bombons/cad-eggbot/progetto/1.png

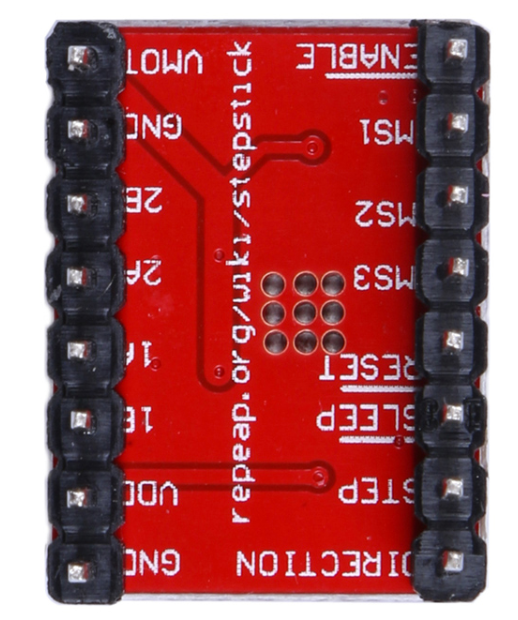
progetto/1.png
