bombons/cad-eggbot/progetto/2.png

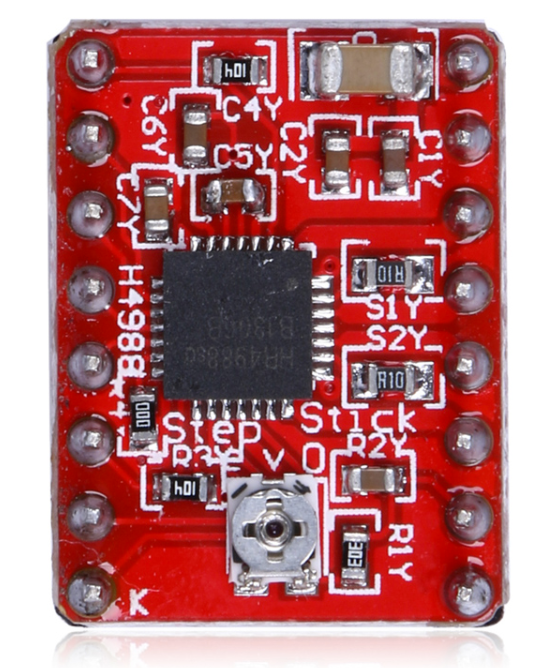
progetto/2.png
