bombons/cad-eggbot/progetto/6pin_header.SLDASM

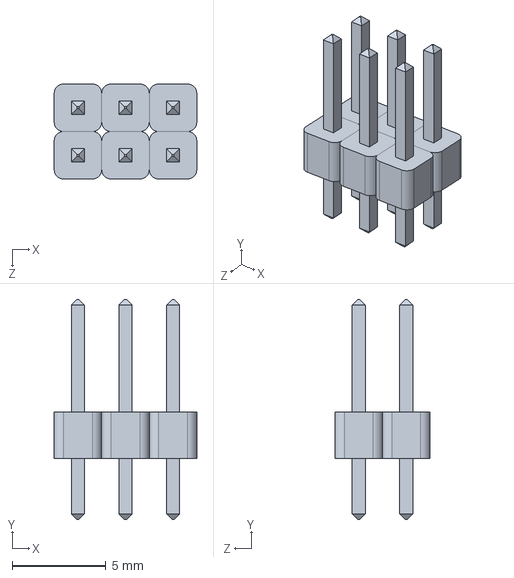
[picture p24: CAD file, 2019-10-07]
progetto/6pin_header.SLDASM
7.62 x 11.8 x 5.08 mm
pin_header x 2
