bombons/cad-eggbot/progetto/statore_spazzole.SLDPRT

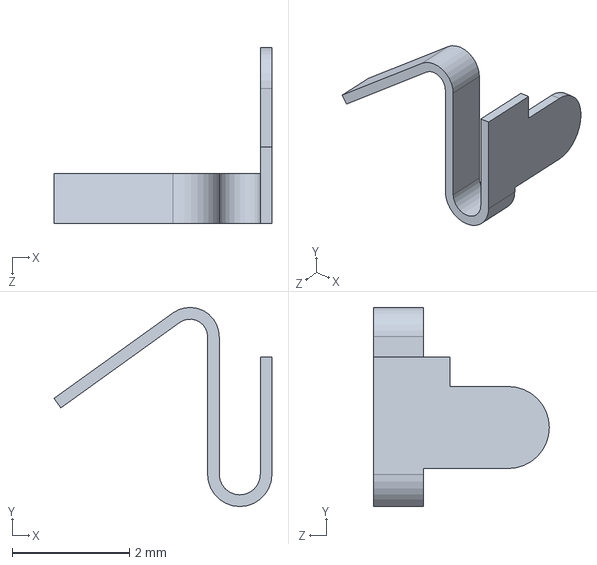
[picture p25: CAD file, 2019-10-07]
progetto/statore_spazzole.SLDPRT
3.72 x 3.40 x 3.00 mm
