bombons/cad-eggbot/progetto/dietro.SLDPRT

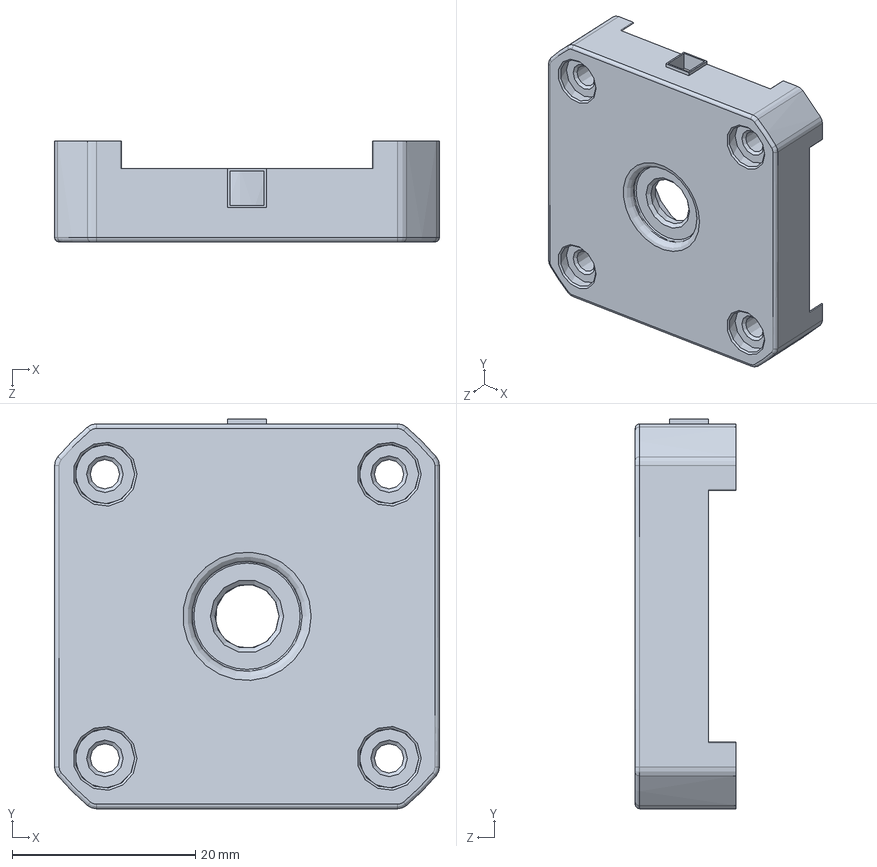
[picture p26: CAD file, 2019-10-07]
progetto/dietro.SLDPRT
42.0 x 42.5 x 11.0 mm
