bombons/cad-eggbot/progetto/pomello_barra_filettata.SLDPRT

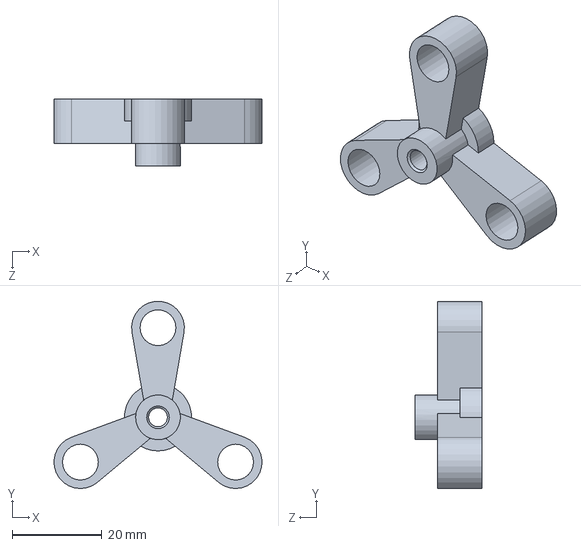
[picture p27: CAD file, 2019-10-07]
progetto/pomello_barra_filettata.SLDPRT
46.4 x 41.8 x 15.0 mm
