bombons/cad-eggbot/progetto/usb_shell.sldprt

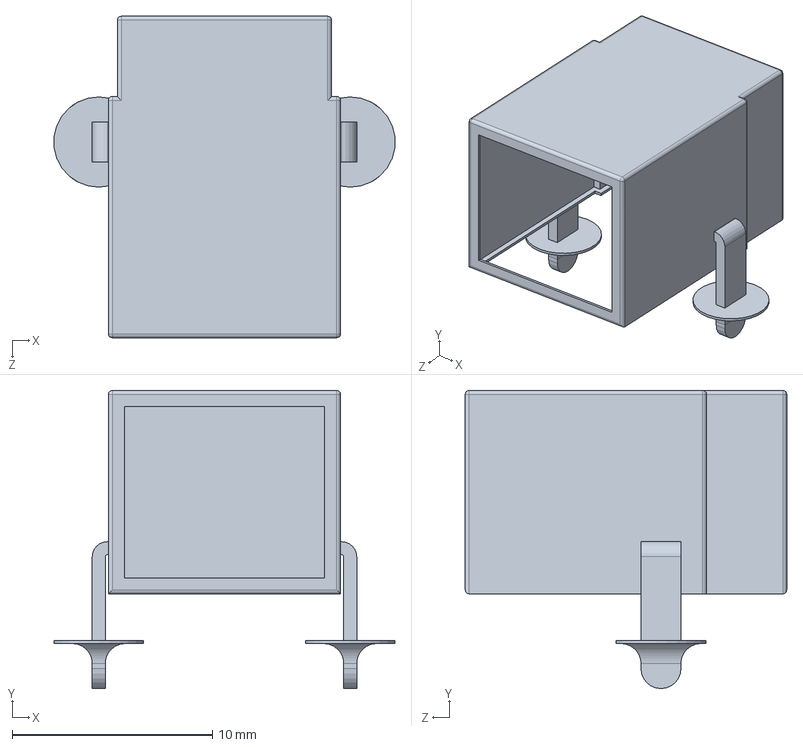
[picture p28: CAD file, 2019-10-07]
progetto/usb_shell.sldprt
17.0 x 14.9 x 16.0 mm
