bombons/cad-eggbot/progetto/jack_alimentazione.SLDPRT

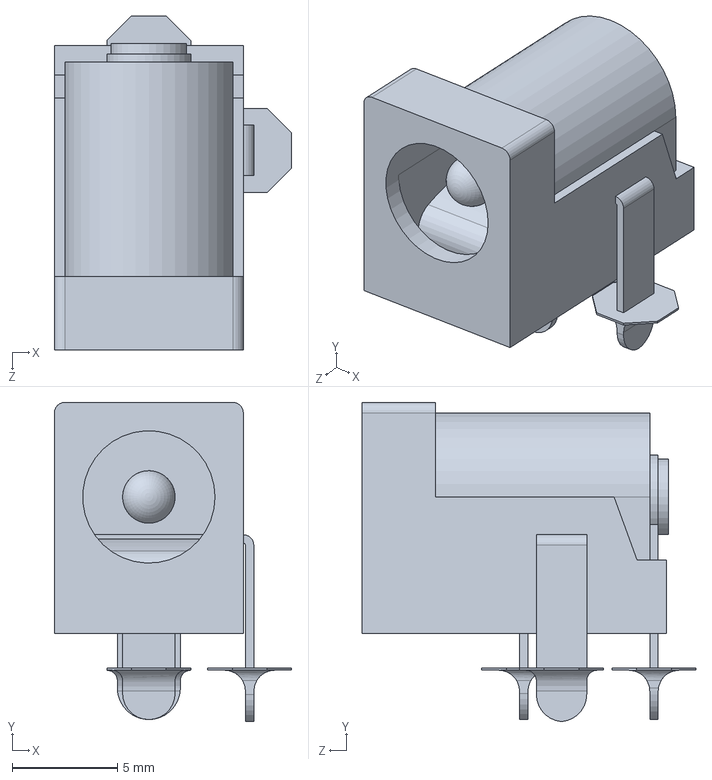
[picture p29: CAD file, 2019-10-07]
progetto/jack_alimentazione.SLDPRT
11.3 x 15.2 x 15.9 mm
