bombons/cad-eggbot/progetto/statore_molla.SLDPRT

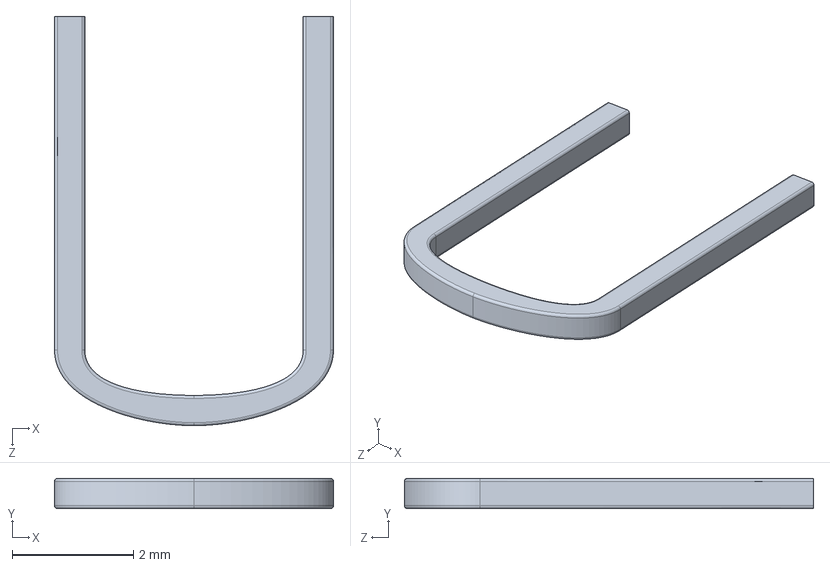
[picture p30: CAD file, 2019-10-07]
progetto/statore_molla.SLDPRT
4.60 x 0.5 x 6.75 mm
