bombons/cad-eggbot/progetto/asse.SLDPRT

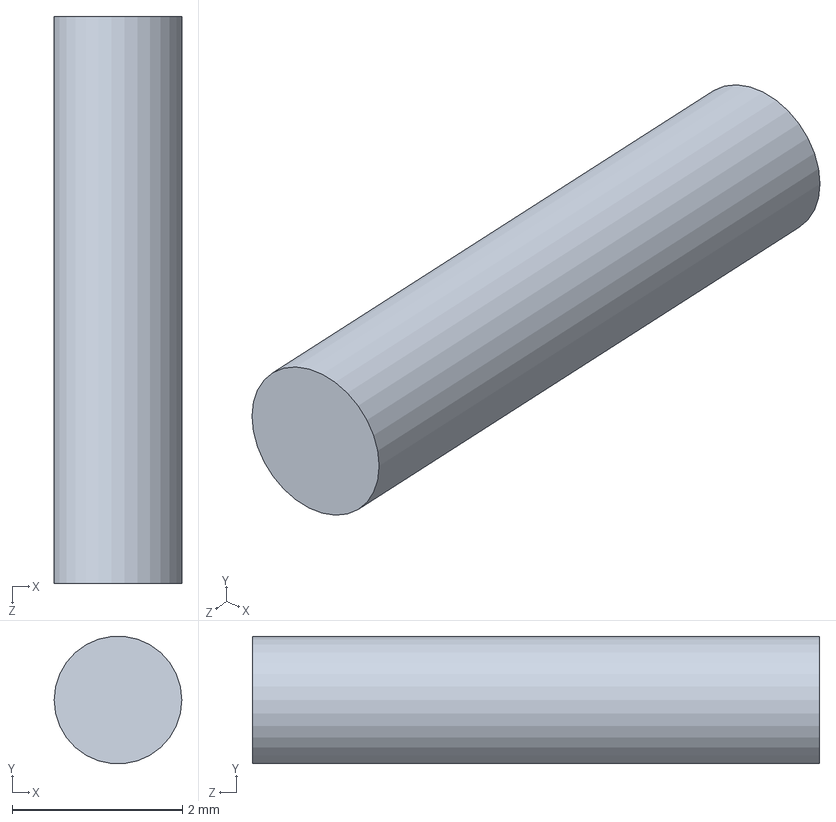
[picture p31: CAD file, 2019-10-07]
progetto/asse.SLDPRT
1.50 x 1.49 x 6.66 mm
