bombons/cad-eggbot/progetto/crystal.SLDPRT

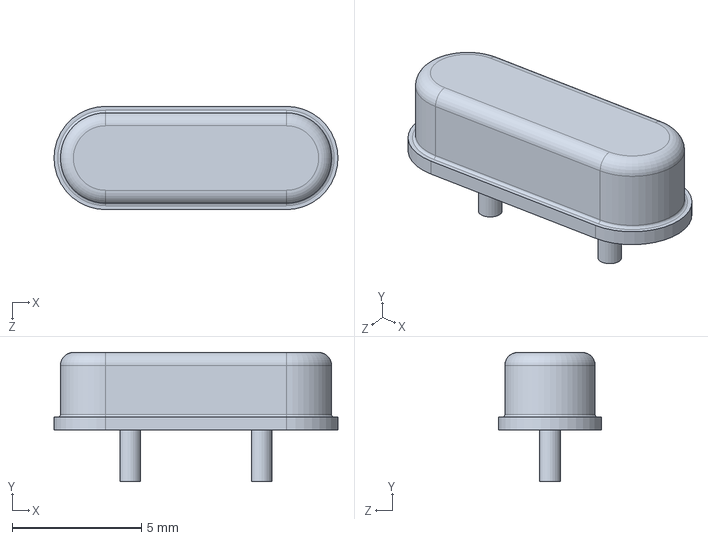
[picture p32: CAD file, 2019-10-07]
progetto/crystal.SLDPRT
11.0 x 5.00 x 4.00 mm
