bombons/cad-eggbot/progetto/asse1.SLDPRT

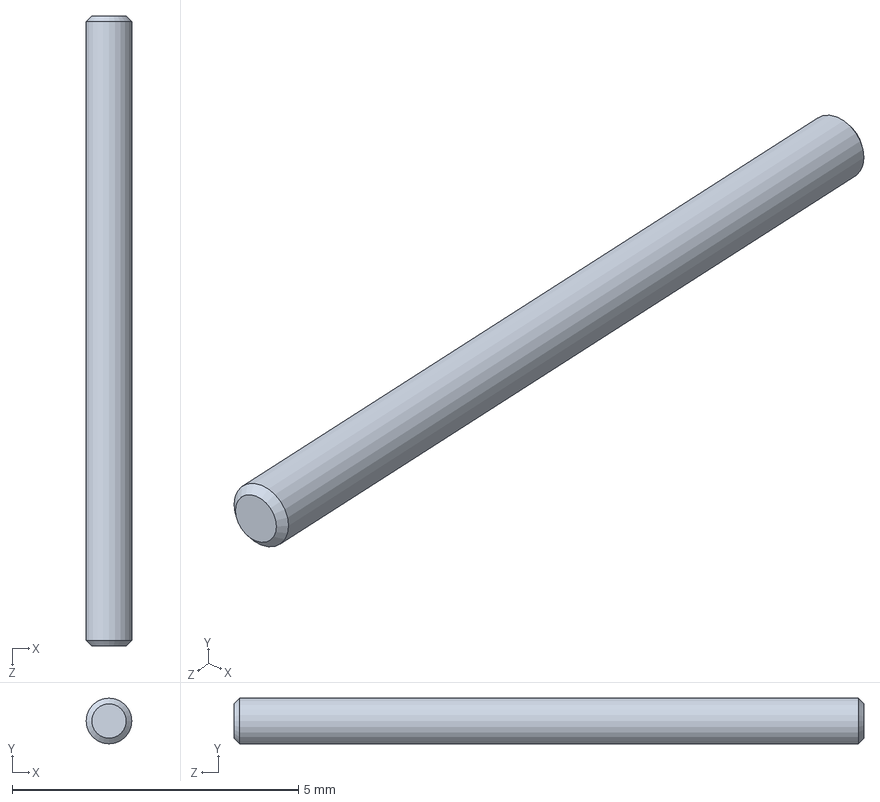
[picture p33: CAD file, 2019-10-07]
progetto/asse1.SLDPRT
0.8 x 0.8 x 11.0 mm
