bombons/cad-eggbot/progetto/board.SLDPRT

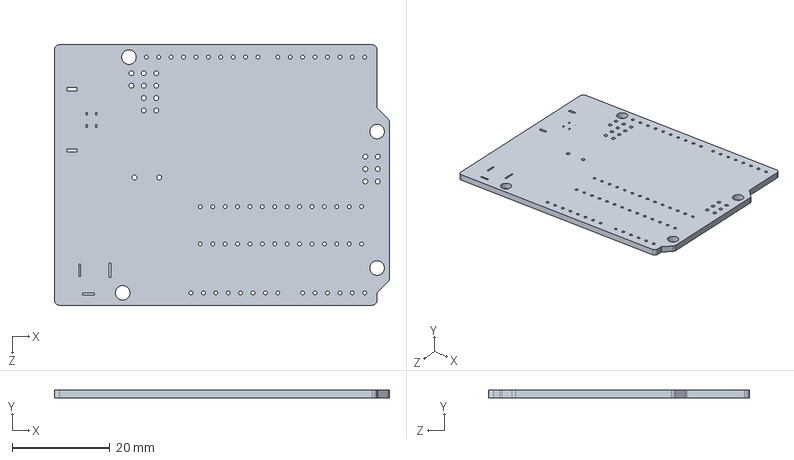
[picture p34: CAD file, 2019-10-07]
progetto/board.SLDPRT
68.6 x 1.65 x 53.3 mm
