bombons/cad-eggbot/progetto/bottone_reset_copertura.SLDPRT

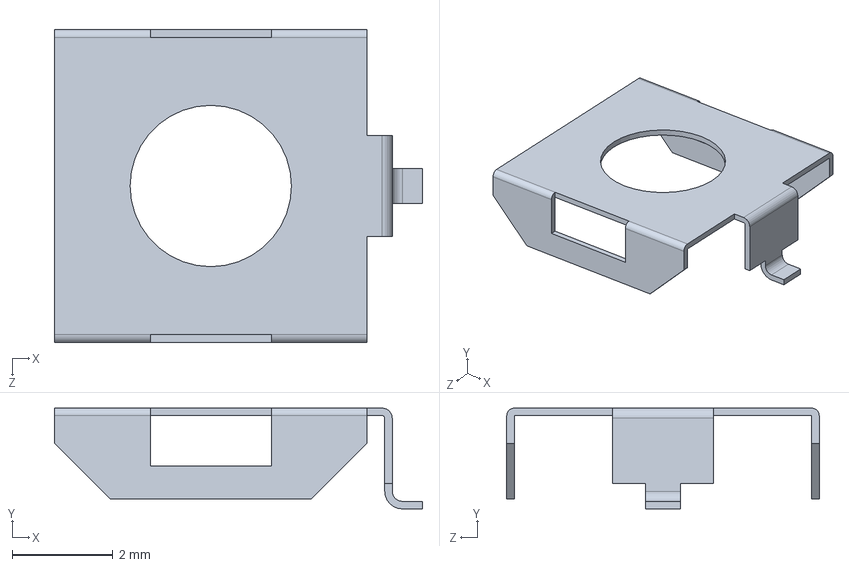
[picture p35: CAD file, 2019-10-07]
progetto/bottone_reset_copertura.SLDPRT
7.30 x 2.00 x 6.20 mm
