bombons/cad-eggbot/progetto/porta_pin.SLDPRT

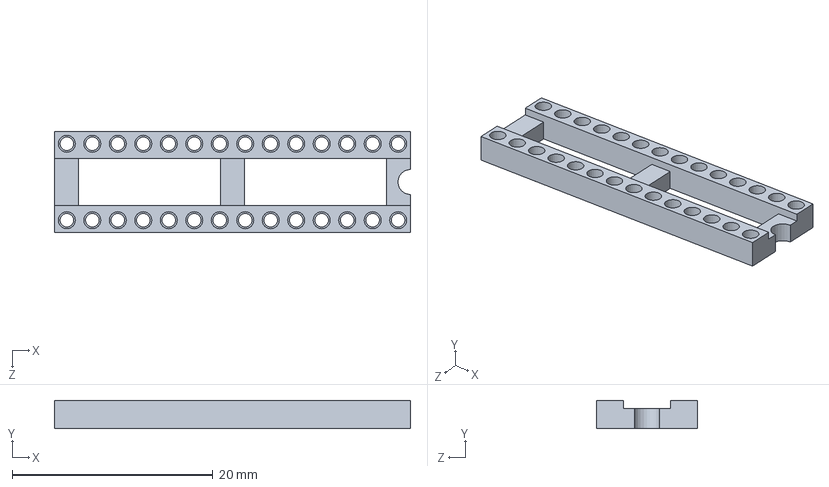
[picture p36: CAD file, 2019-10-07]
progetto/porta_pin.SLDPRT
35.5 x 2.80 x 10.1 mm
