bombons/cad-eggbot/progetto/statore_cuscino1.SLDPRT

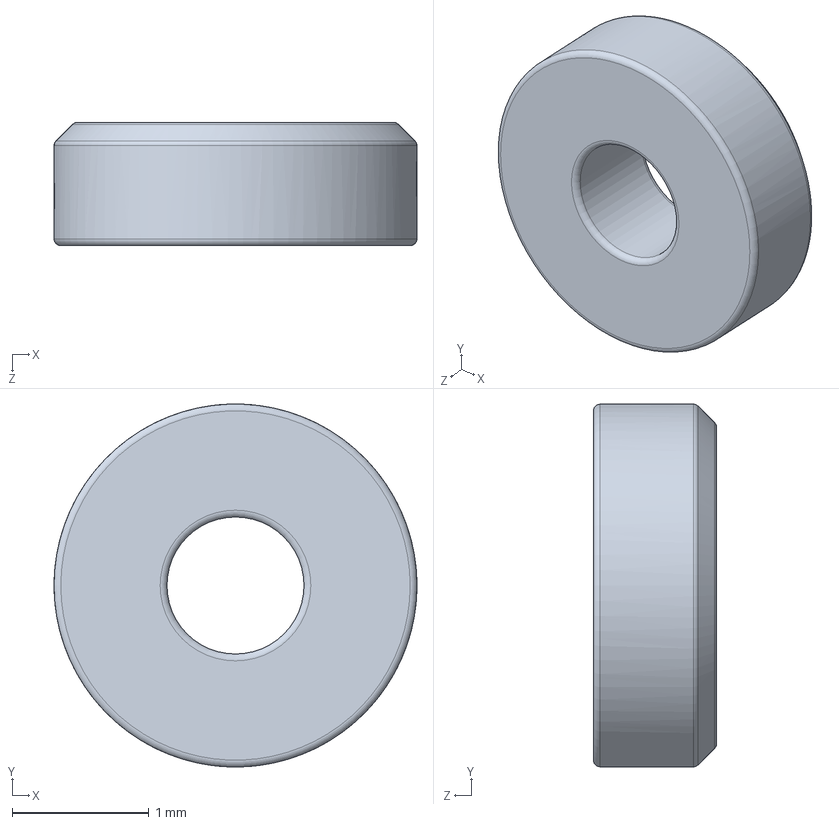
[picture p37: CAD file, 2019-10-07]
progetto/statore_cuscino1.SLDPRT
2.65 x 2.65 x 0.9 mm
