bombons/cad-eggbot/progetto/penna_braccio_fisso.SLDPRT

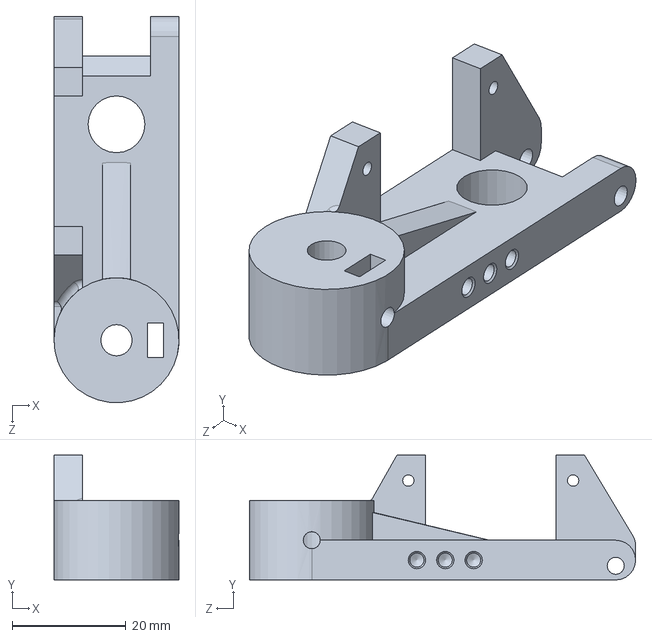
[picture p38: CAD file, 2019-10-07]
progetto/penna_braccio_fisso.SLDPRT
22.0 x 22.0 x 68.0 mm
