bombons/cad-eggbot/progetto/microprocessore.SLDPRT

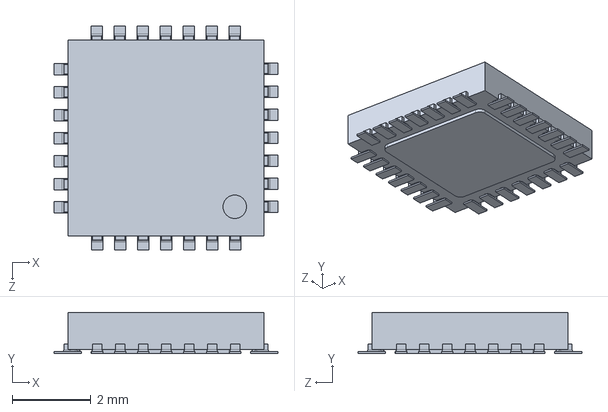
[picture p39: CAD file, 2019-10-07]
progetto/microprocessore.SLDPRT
5.70 x 1.05 x 5.70 mm
