bombons/cad-eggbot/progetto/usb_contatto_su.SLDPRT

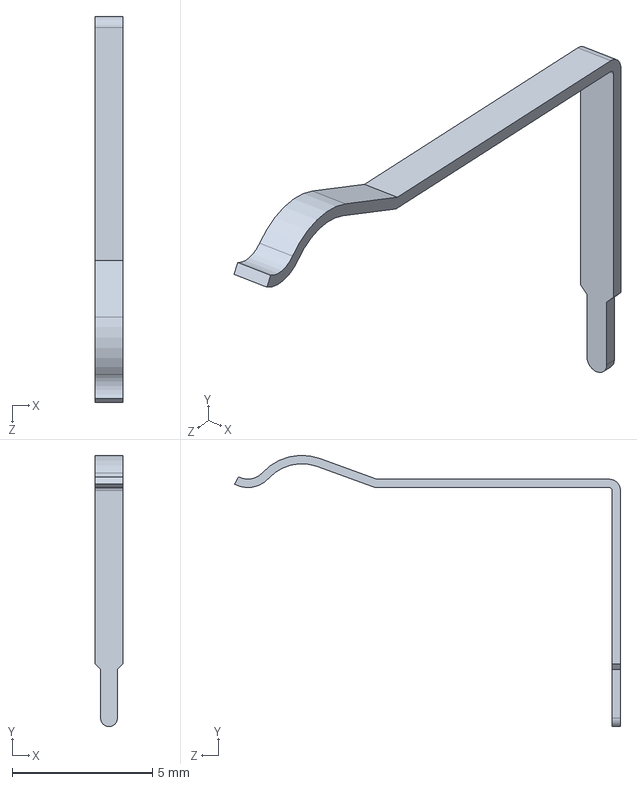
[picture p40: CAD file, 2019-10-07]
progetto/usb_contatto_su.SLDPRT
1.00 x 9.67 x 13.8 mm
