bombons/cad-eggbot/progetto/pot_0.80mm.SLDPRT

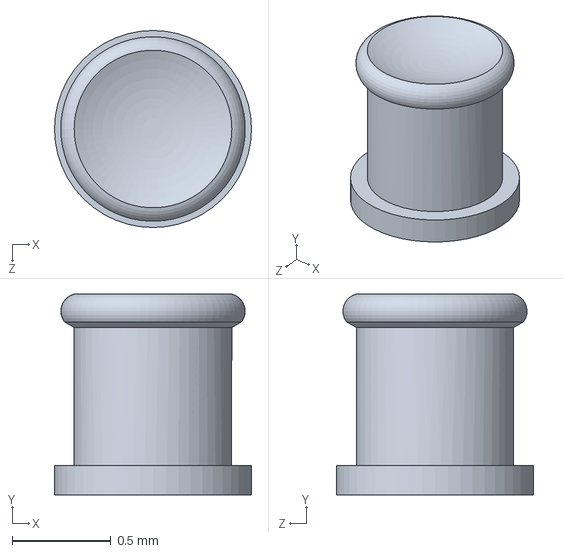
[picture p41: CAD file, 2019-10-07]
progetto/pot_0.80mm.SLDPRT
1.00 x 1.02 x 1.00 mm
