bombons/cad-eggbot/progetto/porta_arduino.SLDPRT

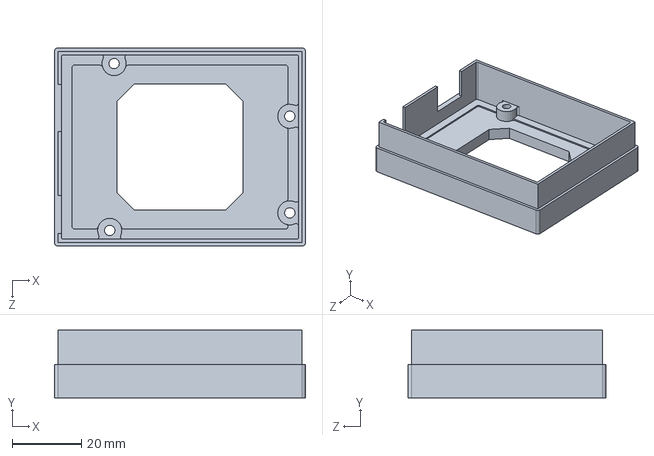
[picture p42: CAD file, 2019-10-07]
progetto/porta_arduino.SLDPRT
72.6 x 19.6 x 57.3 mm
