bombons/cad-eggbot/progetto/1.2_16.SLDPRT

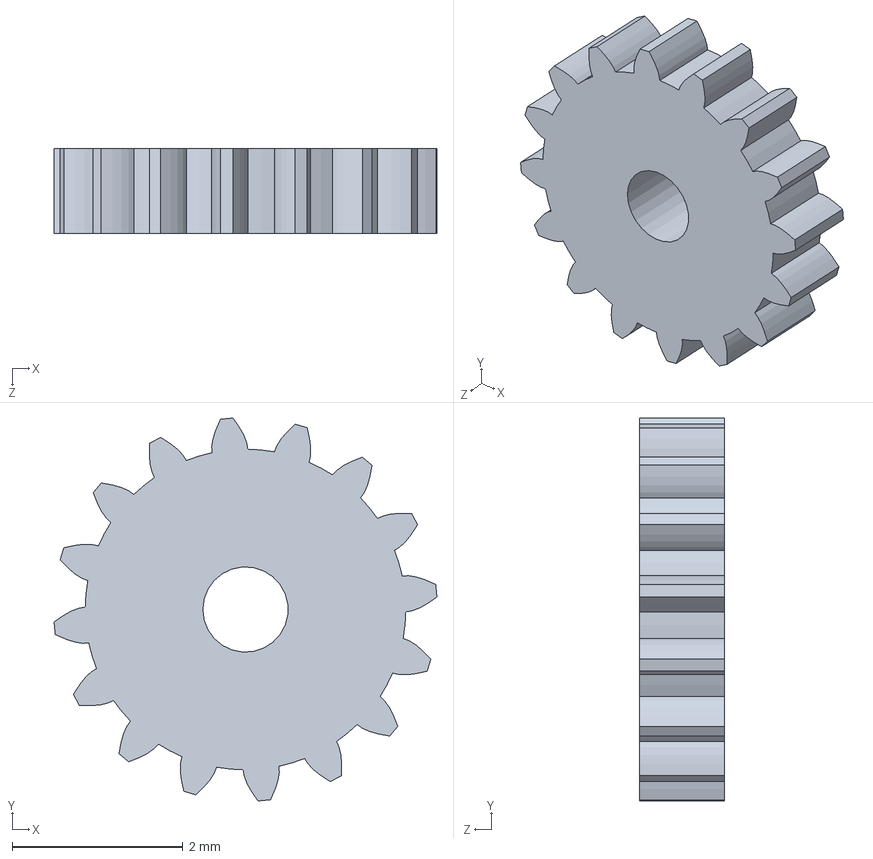
[picture p43: CAD file, 2019-10-07]
progetto/1.2_16.SLDPRT
4.49 x 4.49 x 1.00 mm
