bombons/cad-eggbot/progetto/davanti.SLDPRT

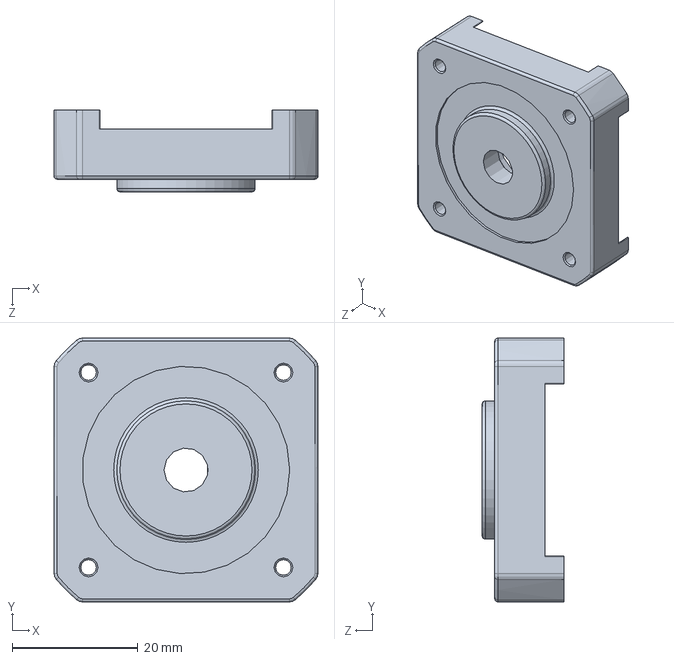
[picture p44: CAD file, 2019-10-07]
progetto/davanti.SLDPRT
42.0 x 42.0 x 13.0 mm
