bombons/cad-eggbot/progetto/1.3_32.SLDPRT

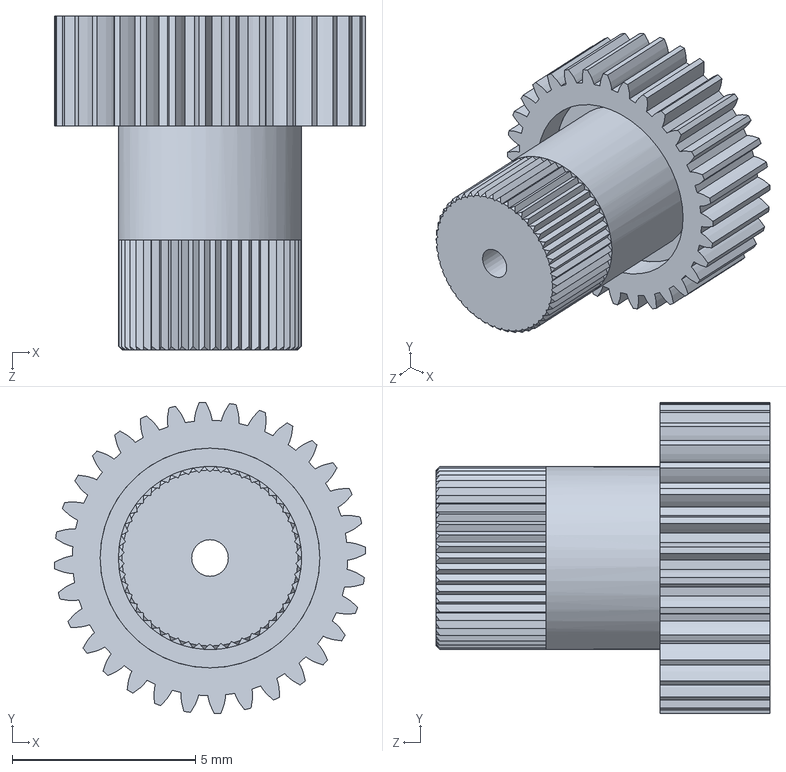
[picture p45: CAD file, 2019-10-07]
progetto/1.3_32.SLDPRT
8.50 x 8.50 x 9.12 mm
