bombons/cad-eggbot/progetto/rotore.SLDPRT

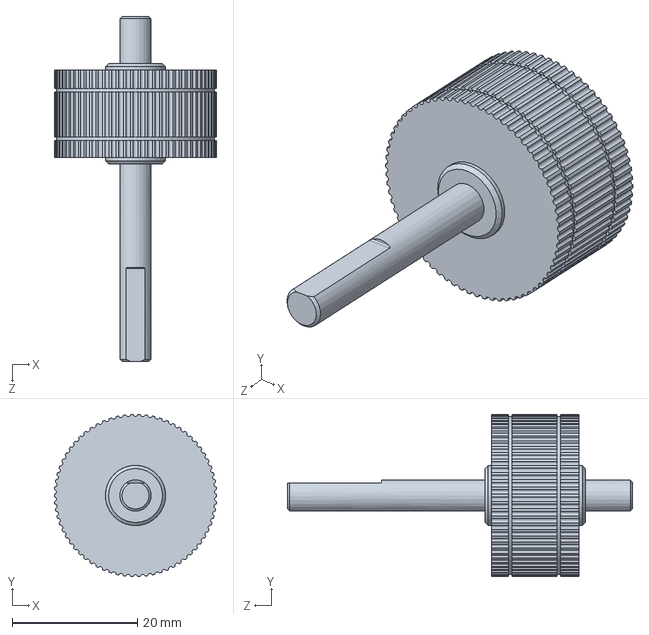
[picture p46: CAD file, 2019-10-07]
progetto/rotore.SLDPRT
25.9 x 25.9 x 55.0 mm
