bombons/cad-eggbot/progetto/rotore_asse.SLDPRT

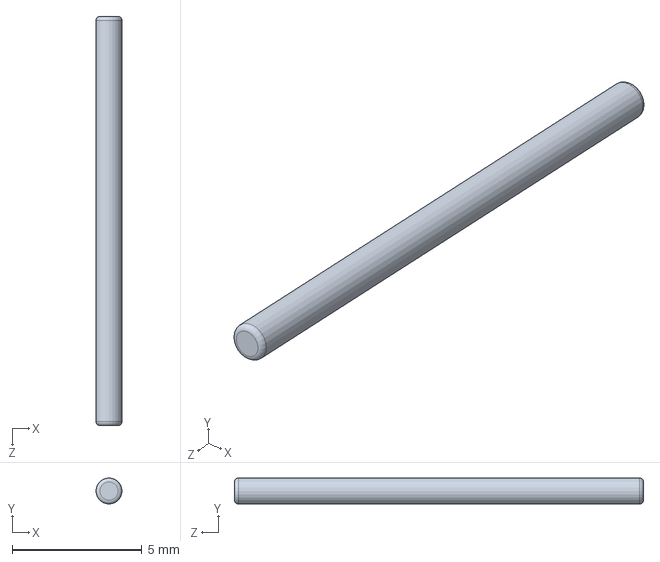
[picture p47: CAD file, 2019-10-07]
progetto/rotore_asse.SLDPRT
1.00 x 1.00 x 15.8 mm
