bombons/cad-eggbot/progetto/nano.SLDPRT

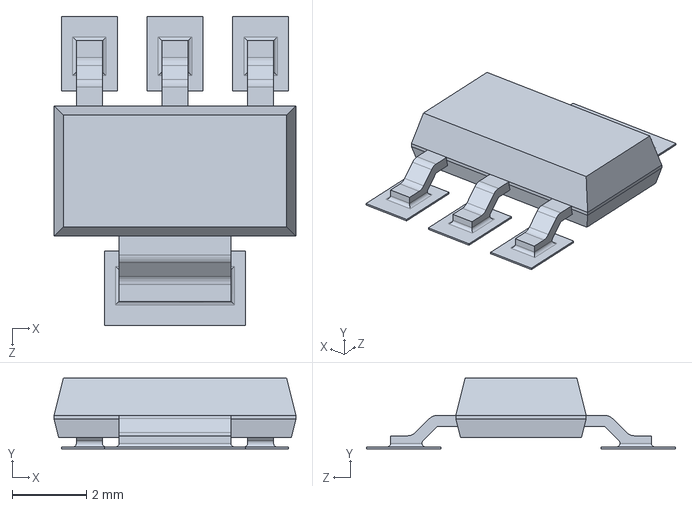
[picture p48: CAD file, 2019-10-07]
progetto/nano.SLDPRT
6.50 x 1.90 x 8.30 mm
