bombons/cad-eggbot/progetto/rotore_rondella1.SLDPRT

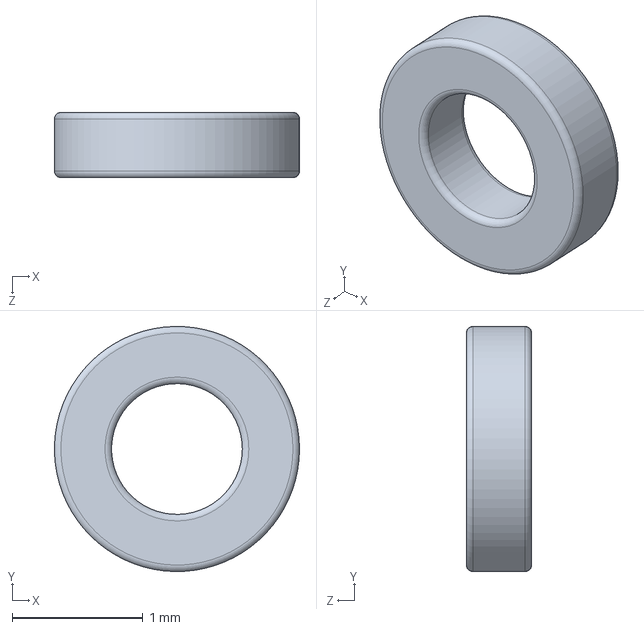
[picture p49: CAD file, 2019-10-07]
progetto/rotore_rondella1.SLDPRT
1.87 x 1.87 x 0.5 mm
