bombons/cad-eggbot/progetto/pot_perno.SLDPRT

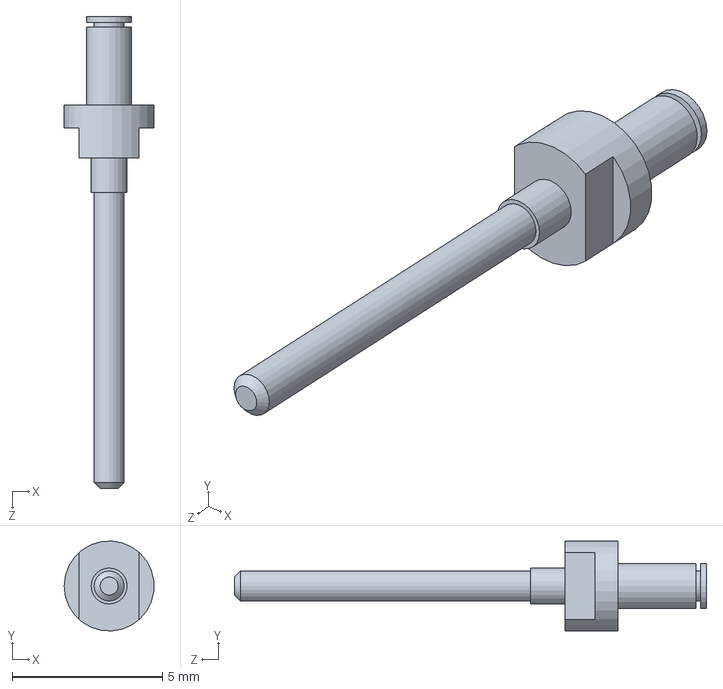
[picture p50: CAD file, 2019-10-07]
progetto/pot_perno.SLDPRT
2.99 x 2.99 x 15.7 mm
