bombons/cad-eggbot/progetto/statore_dietro.SLDPRT

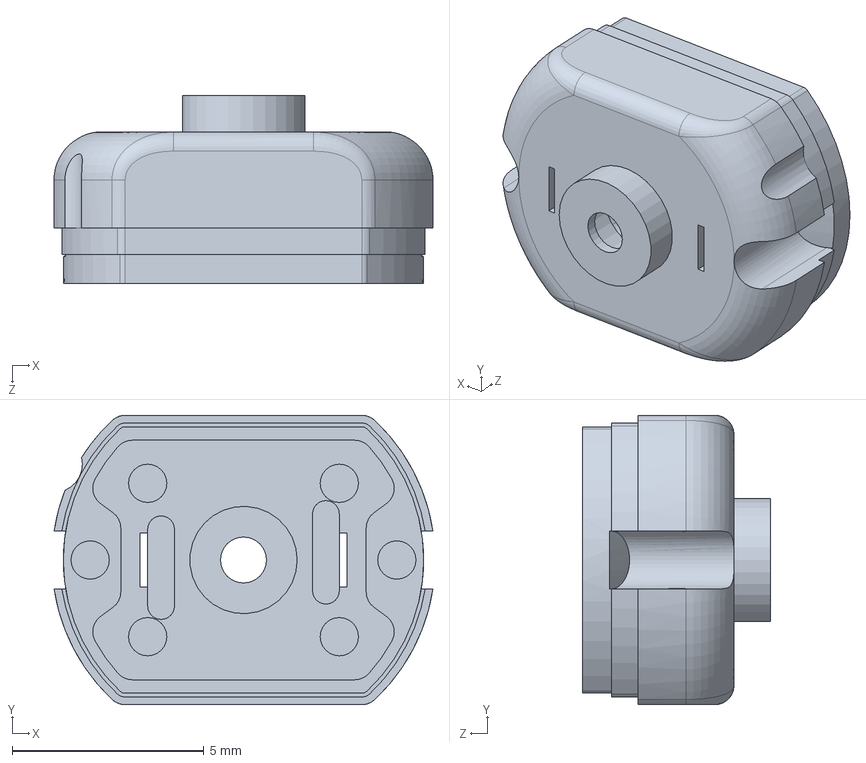
[picture p51: CAD file, 2019-10-07]
progetto/statore_dietro.SLDPRT
9.89 x 7.55 x 4.90 mm
