bombons/cad-eggbot/progetto/603_cap.SLDPRT

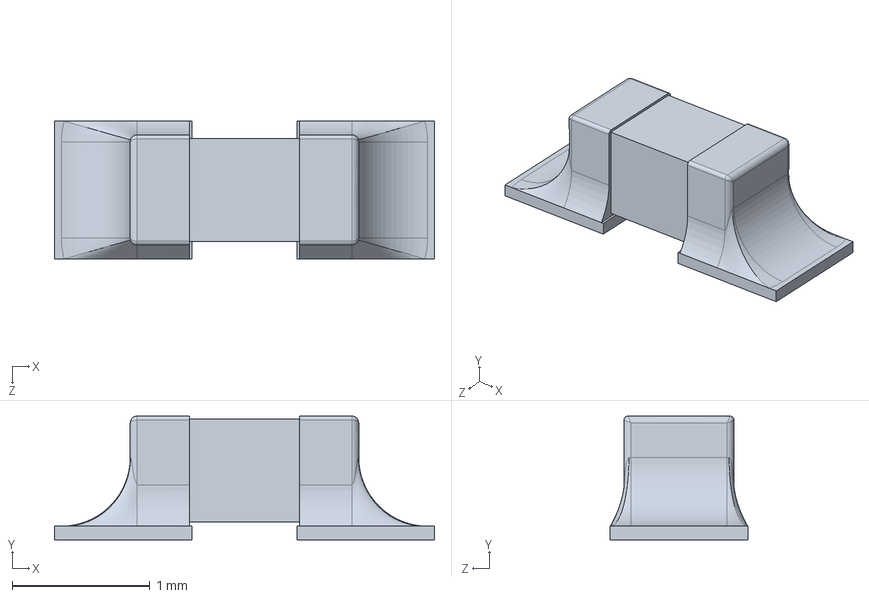
[picture p52: CAD file, 2019-10-07]
progetto/603_cap.SLDPRT
2.76 x 0.9 x 1.00 mm
