bombons/cad-eggbot/progetto/pin.SLDPRT

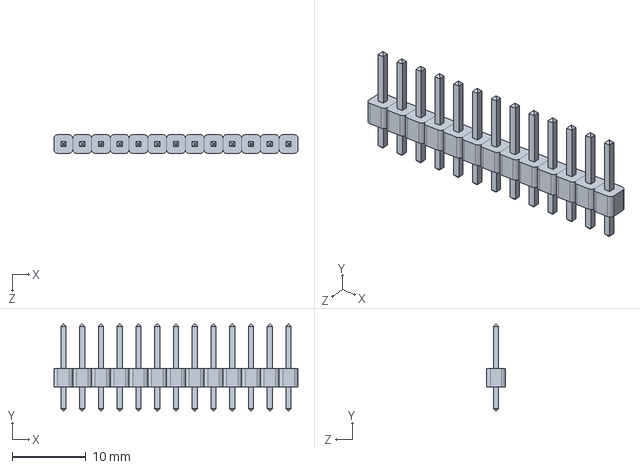
[picture p53: CAD file, 2019-10-07]
progetto/pin.SLDPRT
33.0 x 11.8 x 2.54 mm
