bombons/cad-eggbot/progetto/port_header.SLDPRT

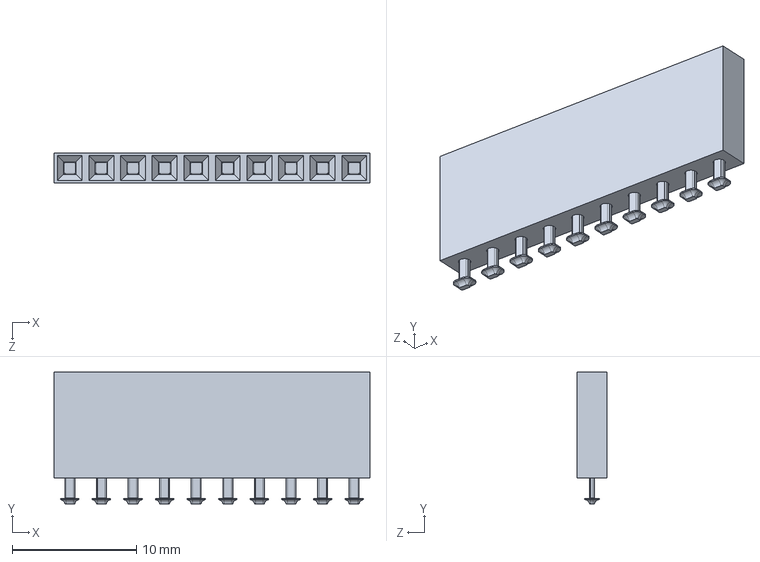
[picture p54: CAD file, 2019-10-07]
progetto/port_header.SLDPRT
25.4 x 10.6 x 2.41 mm
