bombons/cad-eggbot/progetto/pot_0.85mm.SLDPRT

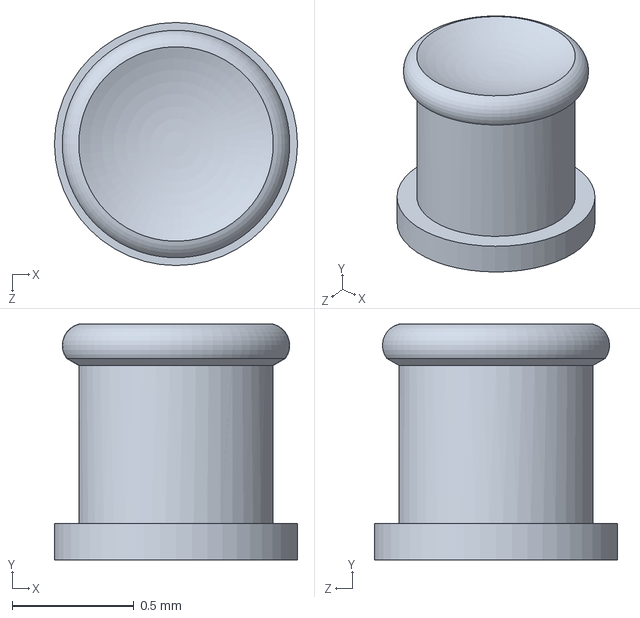
[picture p55: CAD file, 2019-10-07]
progetto/pot_0.85mm.SLDPRT
1.00 x 0.97 x 1.00 mm
