bombons/cad-eggbot/progetto/porta_arduino_coperchio.SLDPRT

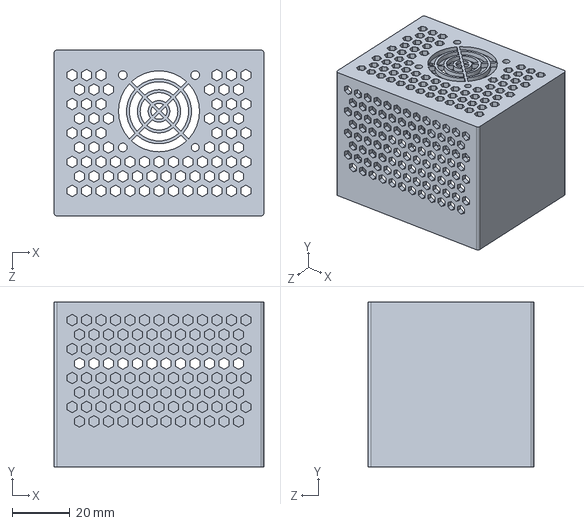
[picture p56: CAD file, 2019-10-07]
progetto/porta_arduino_coperchio.SLDPRT
72.6 x 57.0 x 57.3 mm
