bombons/cad-eggbot/progetto/pot_piastra_contatto.SLDPRT

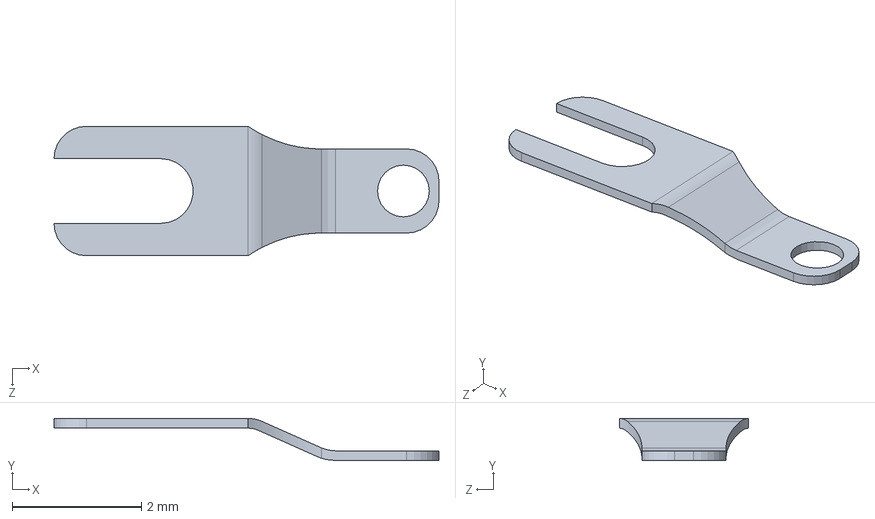
[picture p57: CAD file, 2019-10-07]
progetto/pot_piastra_contatto.SLDPRT
5.95 x 0.65 x 2.00 mm
