bombons/cad-eggbot/progetto/ssot.SLDPRT

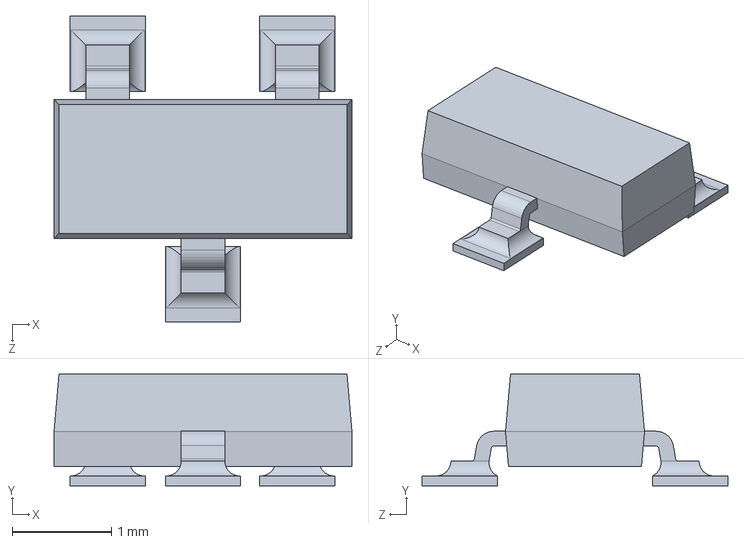
[picture p58: CAD file, 2019-10-07]
progetto/ssot.SLDPRT
3.00 x 1.12 x 3.08 mm
