bombons/cad-eggbot/progetto/pot_contatto_sopra.SLDPRT

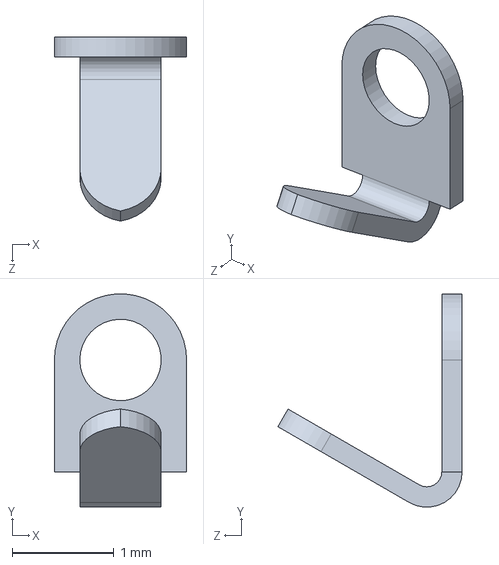
[picture p59: CAD file, 2019-10-07]
progetto/pot_contatto_sopra.SLDPRT
1.30 x 2.09 x 1.81 mm
