bombons/cad-eggbot/progetto/resistenza.SLDPRT

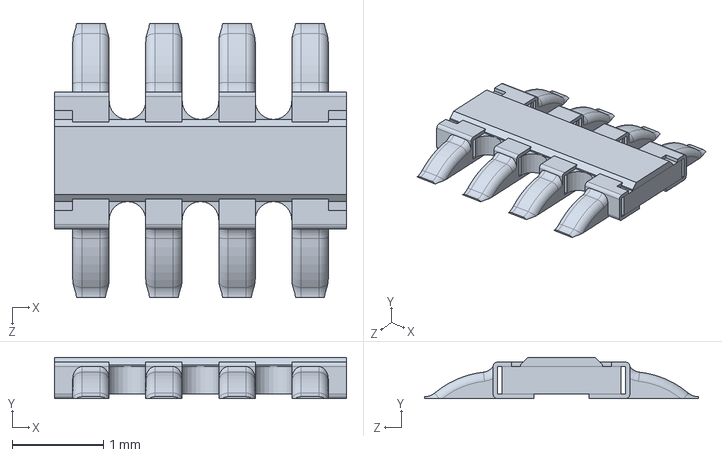
[picture p60: CAD file, 2019-10-07]
progetto/resistenza.SLDPRT
3.20 x 0.45 x 3.00 mm
