bombons/cad-eggbot/progetto/alimentatore.SLDPRT

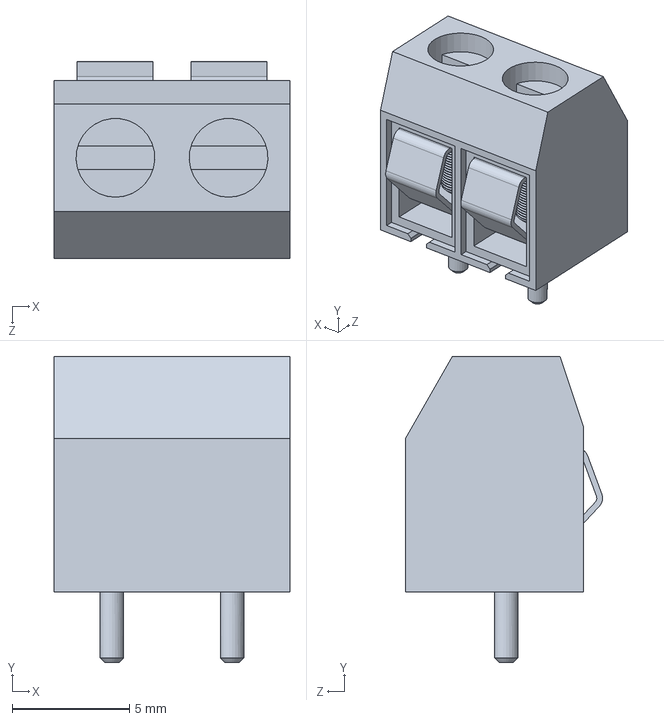
[picture p61: CAD file, 2019-10-07]
progetto/alimentatore.SLDPRT
10.0 x 13.1 x 8.41 mm
