bombons/cad-eggbot/progetto/dissipatore.SLDPRT

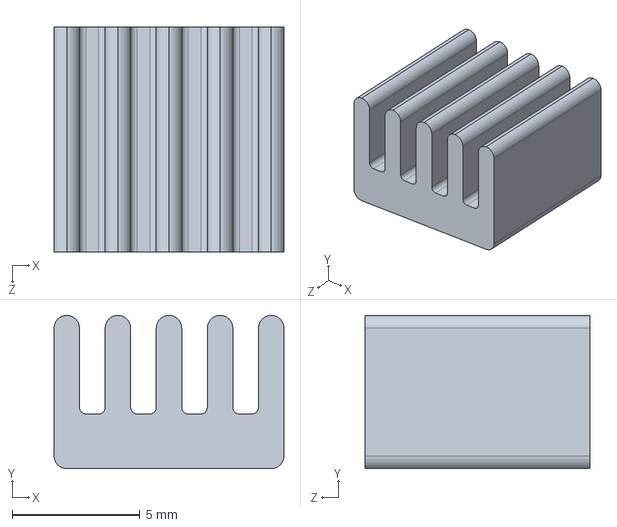
[picture p62: CAD file, 2019-10-07]
progetto/dissipatore.SLDPRT
9.00 x 6.00 x 8.80 mm
