bombons/cad-eggbot/progetto/pot_corpo.SLDPRT

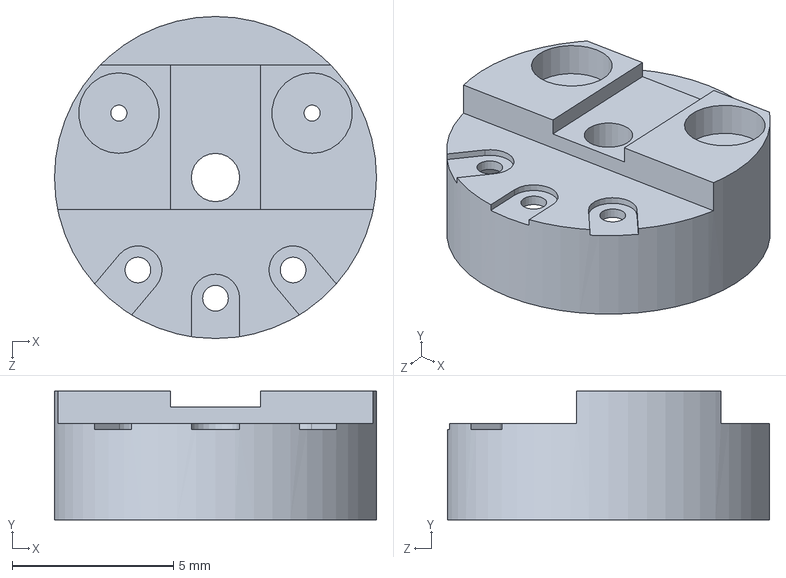
[picture p63: CAD file, 2019-10-07]
progetto/pot_corpo.SLDPRT
10.0 x 4.00 x 10.0 mm
