bombons/cad-eggbot/progetto/reggi_cusinetto.SLDPRT

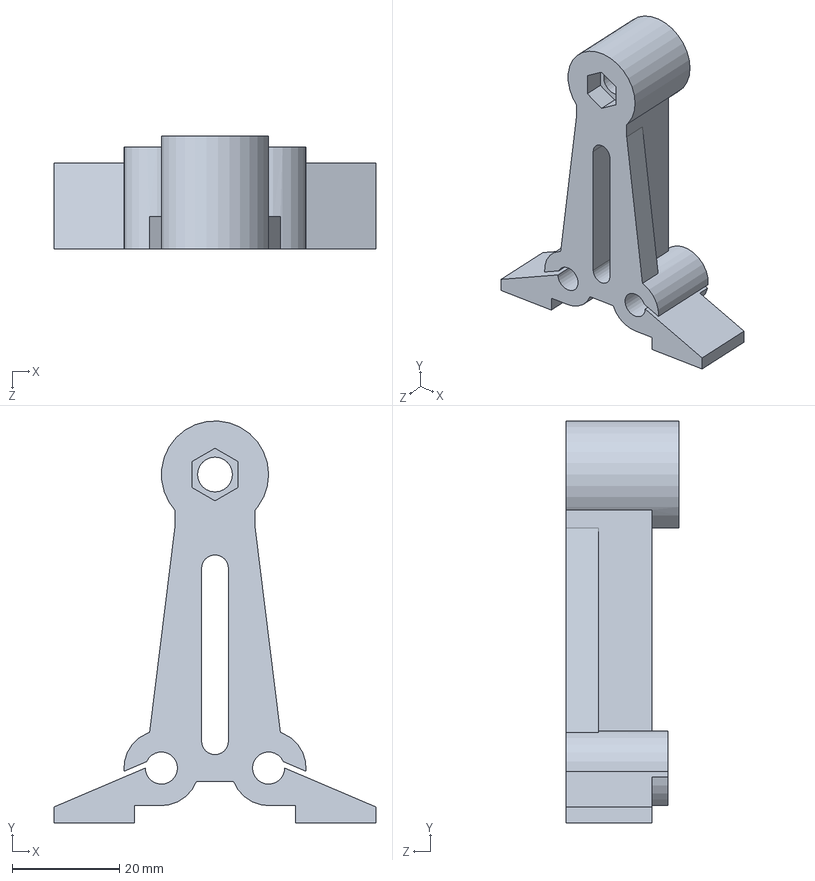
[picture p64: CAD file, 2019-10-07]
progetto/reggi_cusinetto.SLDPRT
60.0 x 75.0 x 21.0 mm
