bombons/cad-eggbot/progetto/resistenza2.SLDPRT

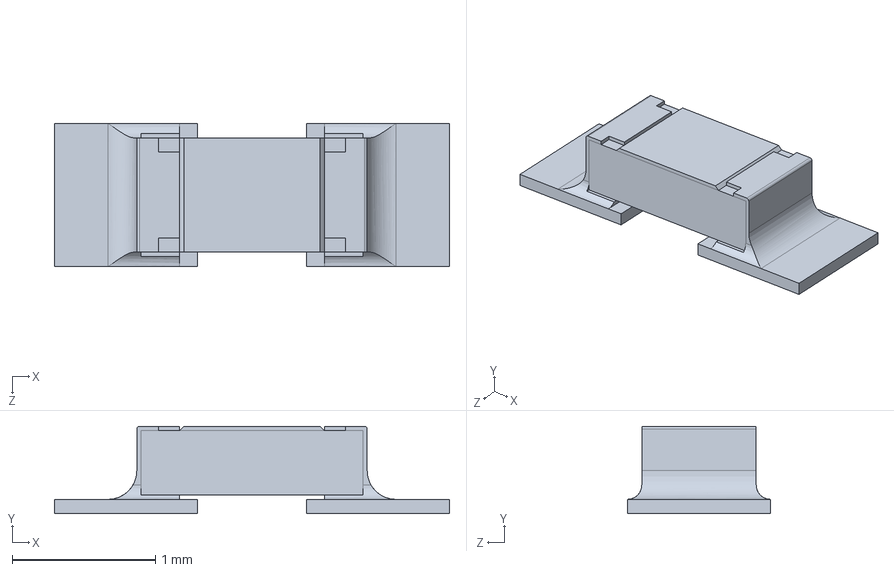
[picture p65: CAD file, 2019-10-07]
progetto/resistenza2.SLDPRT
2.76 x 0.61 x 1.00 mm
