bombons/cad-eggbot/progetto/penna_braccio_mobile.SLDPRT

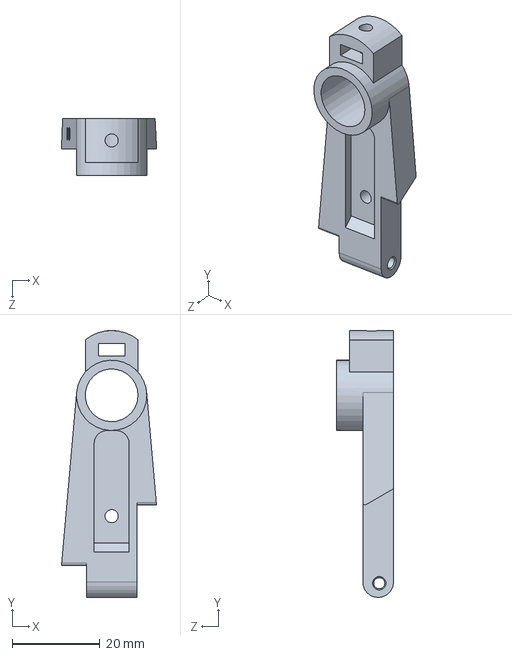
[picture p66: CAD file, 2019-10-07]
progetto/penna_braccio_mobile.SLDPRT
21.6 x 60.8 x 13.0 mm
