bombons/cad-eggbot/progetto/pin_header.SLDPRT

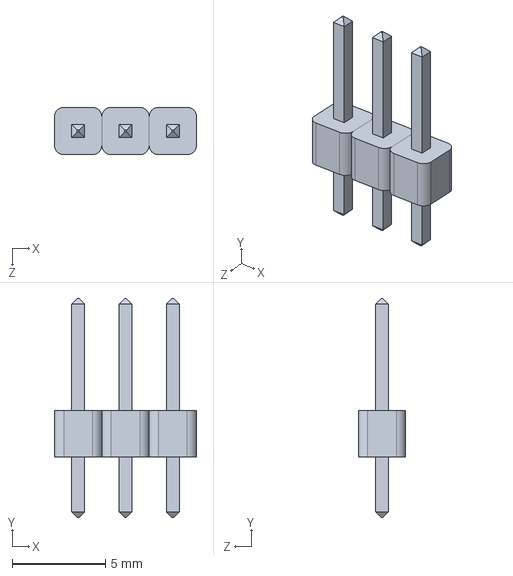
[picture p67: CAD file, 2019-10-07]
progetto/pin_header.SLDPRT
7.62 x 11.8 x 2.54 mm
