bombons/cad-eggbot/progetto/usb_contatto_giu.SLDPRT

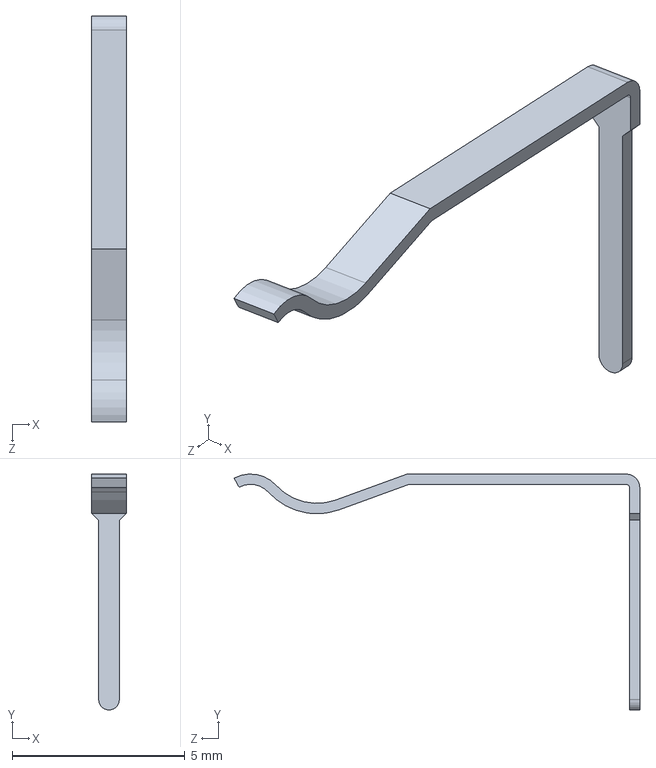
[picture p68: CAD file, 2019-10-07]
progetto/usb_contatto_giu.SLDPRT
1.00 x 6.84 x 11.8 mm
