bombons/cad-eggbot/progetto/led.SLDPRT

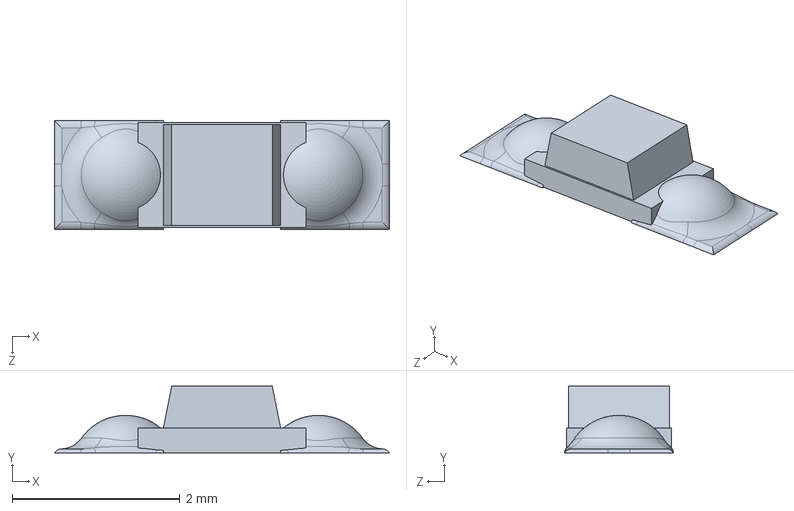
[picture p69: CAD file, 2019-10-07]
progetto/led.SLDPRT
4.00 x 0.8 x 1.30 mm
