bombons/cad-eggbot/progetto/1.1_32.SLDPRT

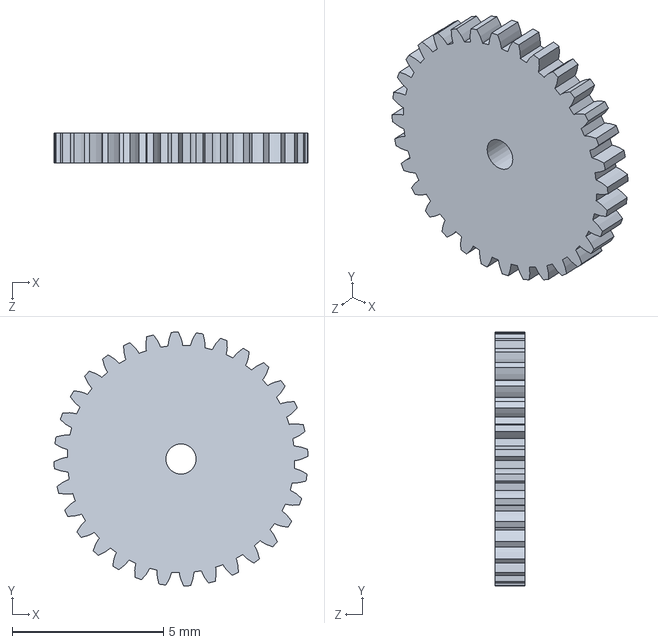
[picture p70: CAD file, 2019-10-07]
progetto/1.1_32.SLDPRT
8.40 x 8.40 x 1.00 mm
