bombons/cad-eggbot/progetto/mf.SLDPRT

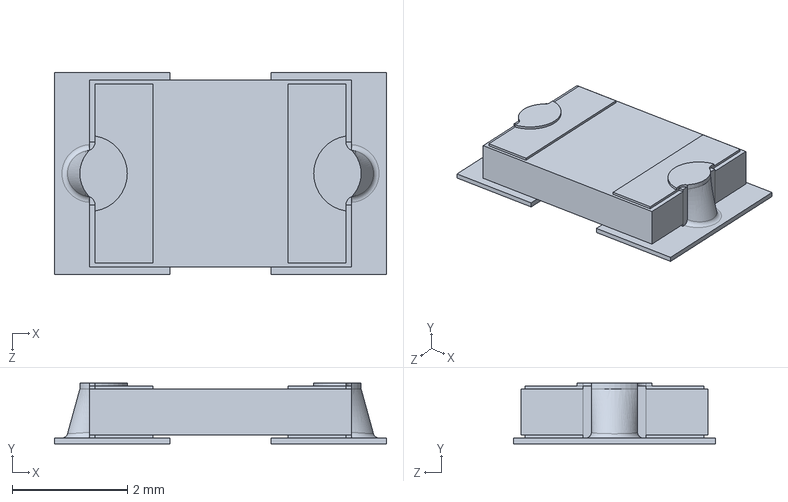
[picture p71: CAD file, 2019-10-07]
progetto/mf.SLDPRT
5.76 x 1.05 x 3.50 mm
