bombons/cad-eggbot/progetto/attacco.SLDPRT

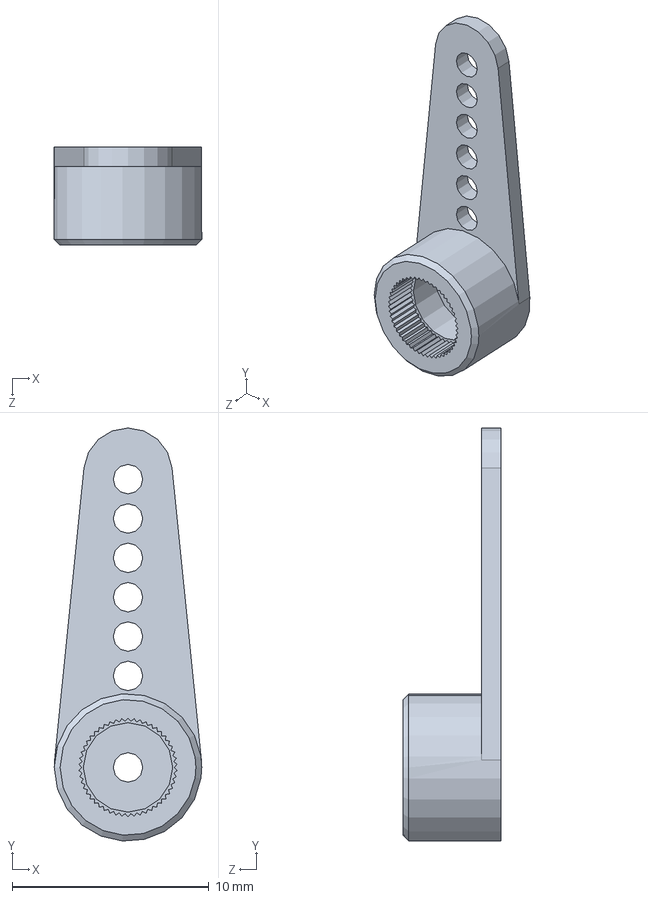
[picture p72: CAD file, 2019-10-07]
progetto/attacco.SLDPRT
7.50 x 21.0 x 5.00 mm
