bombons/cad-eggbot/progetto/rotore_spazzole.SLDPRT

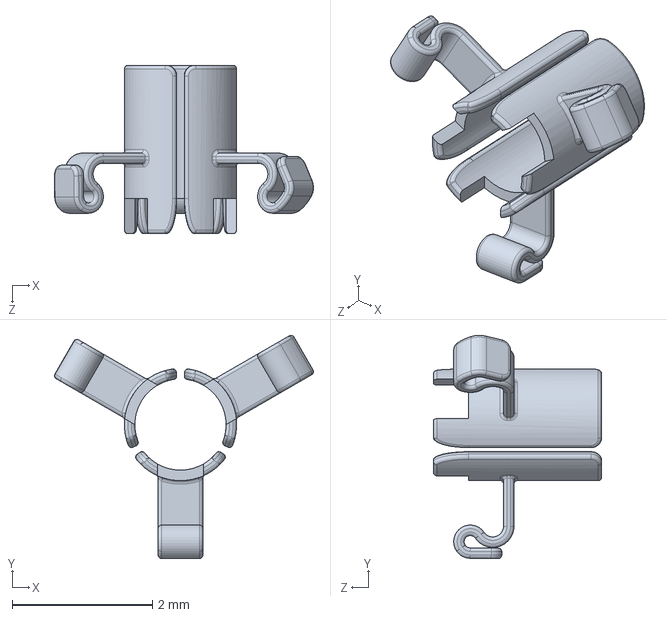
[picture p73: CAD file, 2019-10-07]
progetto/rotore_spazzole.SLDPRT
3.69 x 3.18 x 2.40 mm
