bombons/cad-eggbot/progetto/rotore_rondella2.SLDPRT

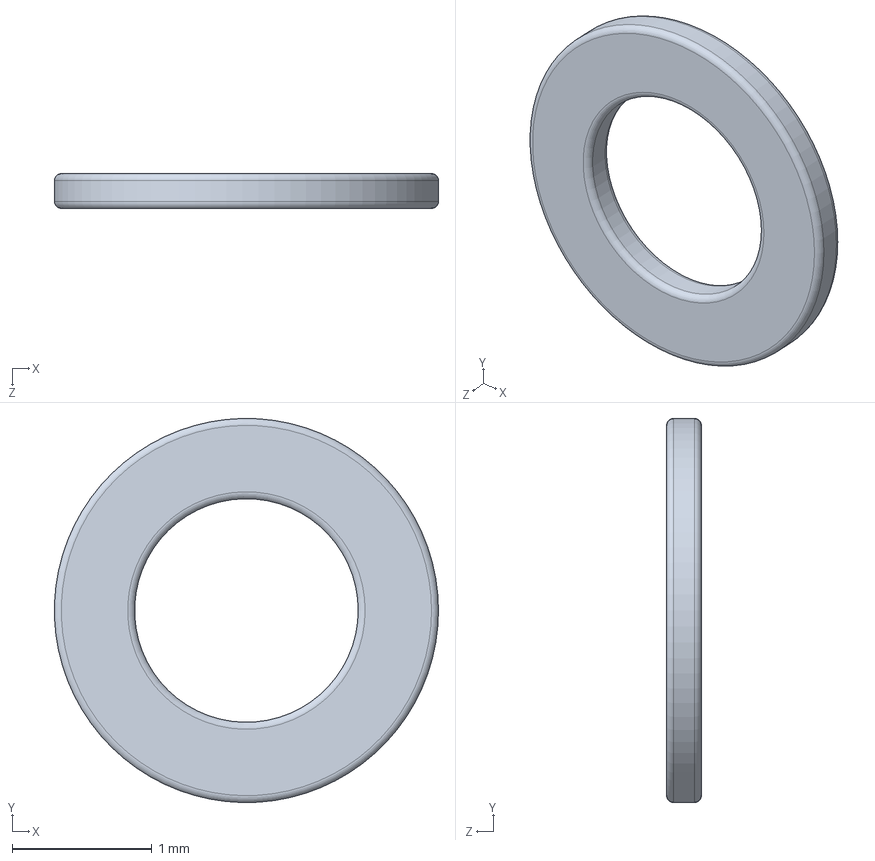
[picture p74: CAD file, 2019-10-07]
progetto/rotore_rondella2.SLDPRT
2.75 x 2.75 x 0.25 mm
