bombons/cad-eggbot/progetto/shell3.SLDPRT

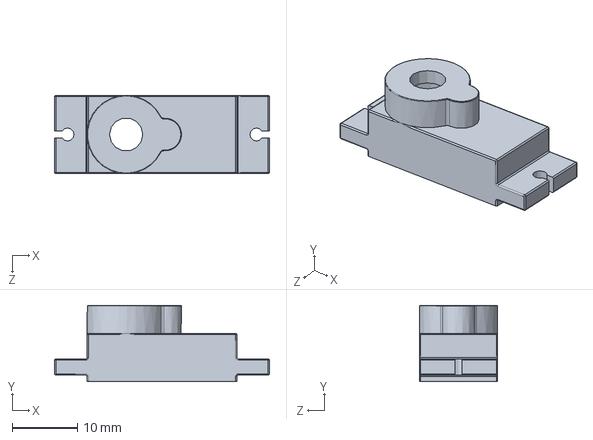
[picture p75: CAD file, 2019-10-07]
progetto/shell3.SLDPRT
33.0 x 11.7 x 12.0 mm
