bombons/cad-eggbot/progetto/atmega16.SLDPRT

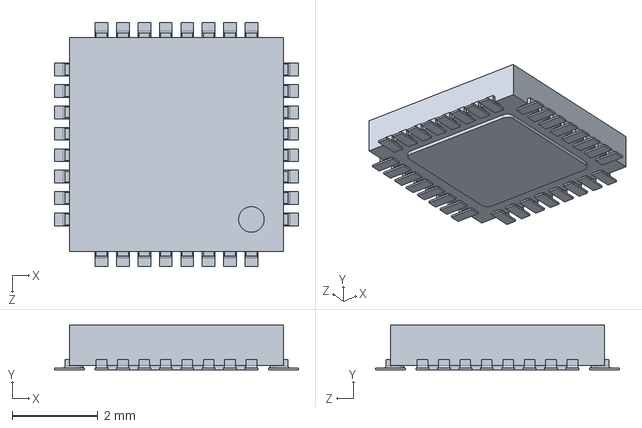
[picture p76: CAD file, 2019-10-07]
progetto/atmega16.SLDPRT
5.70 x 1.05 x 5.70 mm
