bombons/cad-eggbot/progetto/cuscino.SLDPRT

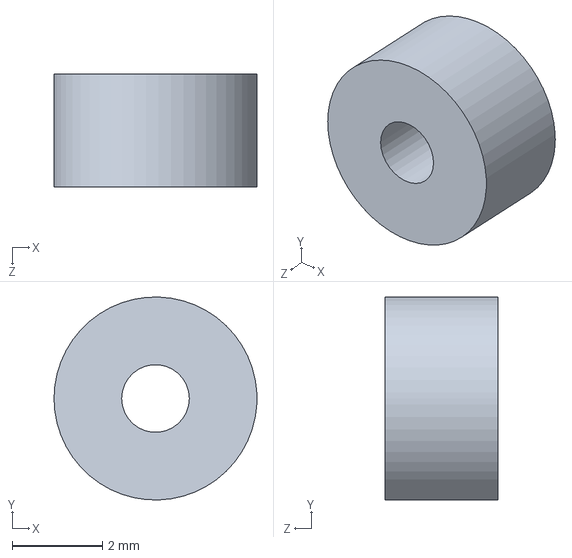
[picture p77: CAD file, 2019-10-07]
progetto/cuscino.SLDPRT
4.50 x 4.50 x 2.50 mm
