bombons/cad-eggbot/progetto/3.1_16.SLDPRT

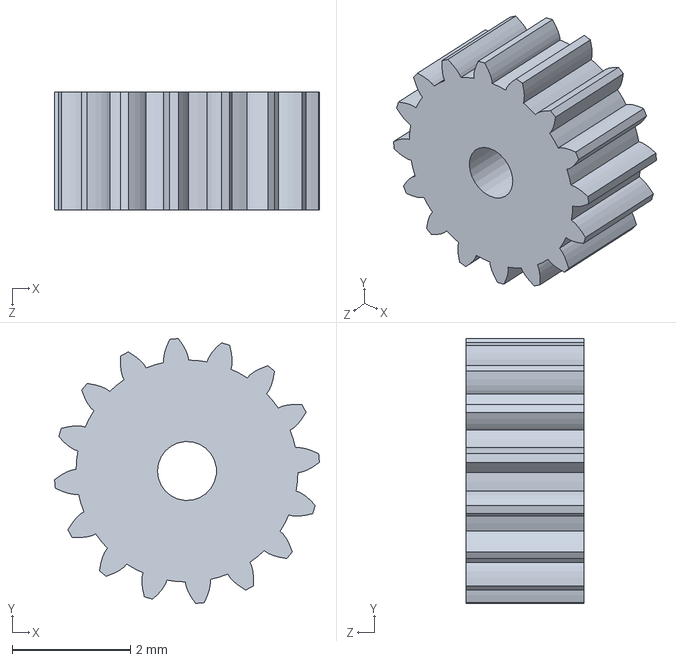
[picture p78: CAD file, 2019-10-07]
progetto/3.1_16.SLDPRT
4.49 x 4.49 x 2.00 mm
