bombons/cad-eggbot/progetto/cnc_board.SLDPRT

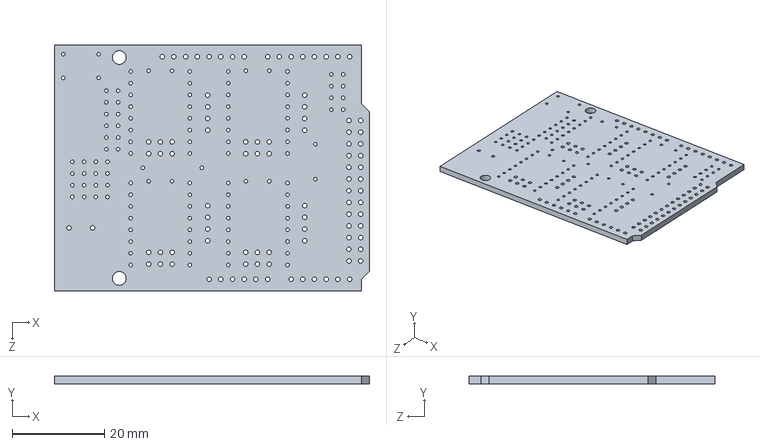
[picture p79: CAD file, 2019-10-07]
progetto/cnc_board.SLDPRT
68.3 x 1.65 x 53.3 mm
