bombons/cad-eggbot/progetto/tieni_uova_cuscino.SLDPRT

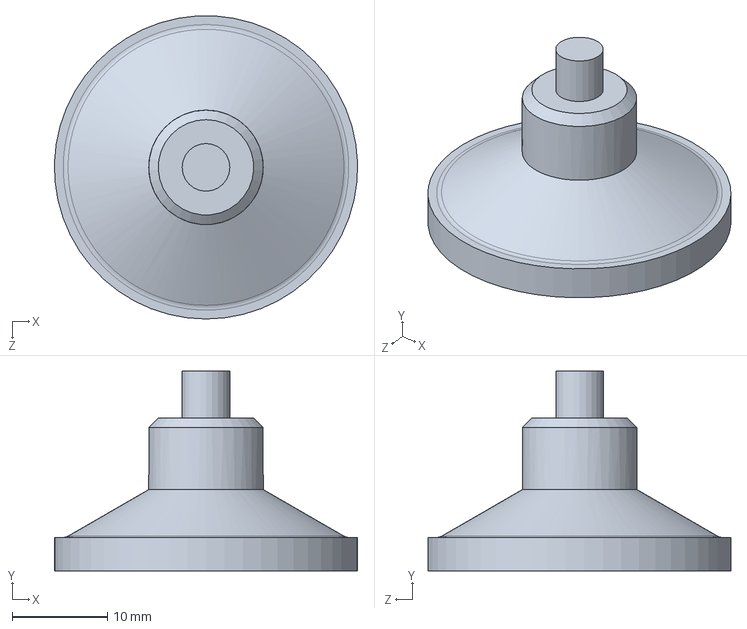
[picture p80: CAD file, 2019-10-07]
progetto/tieni_uova_cuscino.SLDPRT
31.8 x 20.9 x 31.7 mm
