bombons/cad-eggbot/progetto/tieni_uova_stepper.SLDPRT

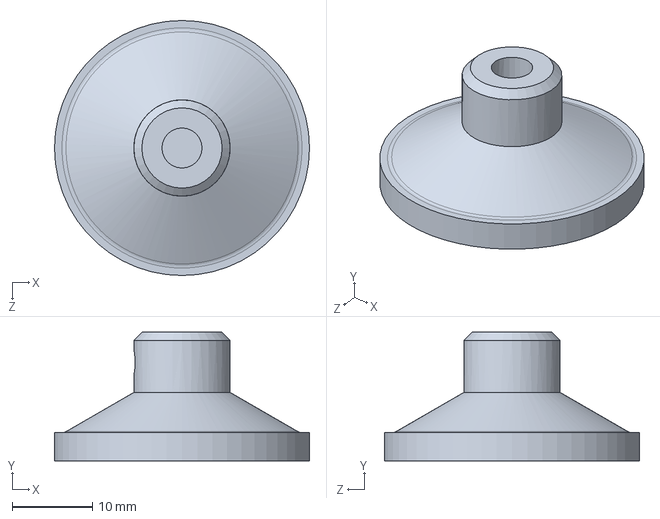
[picture p81: CAD file, 2019-10-07]
progetto/tieni_uova_stepper.SLDPRT
31.8 x 16.0 x 31.8 mm
