bombons/cad-eggbot/progetto/2.4_16.SLDPRT

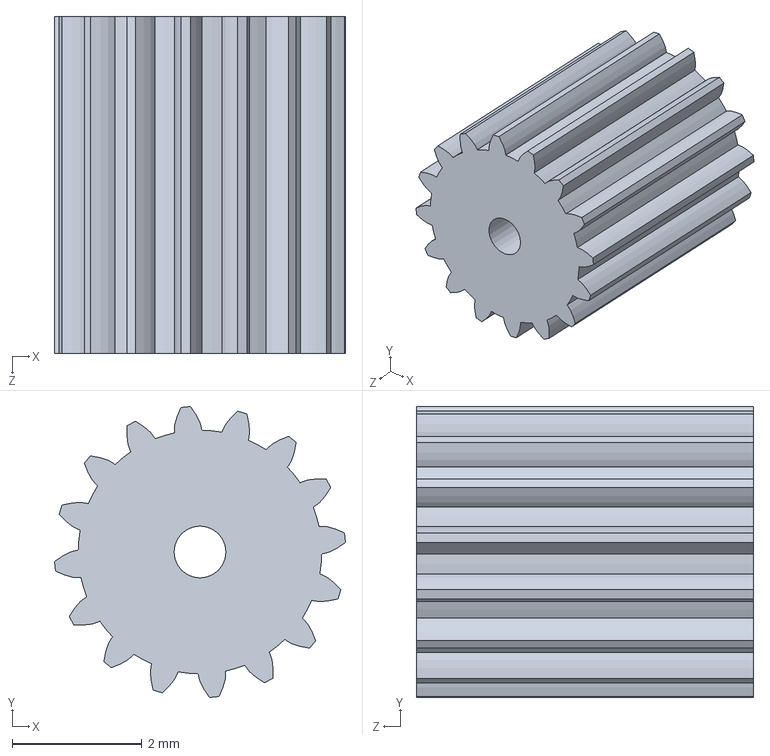
[picture p82: CAD file, 2019-10-07]
progetto/2.4_16.SLDPRT
4.49 x 4.49 x 5.20 mm
