bombons/cad-eggbot/progetto/pot_contatto_sotto.SLDPRT

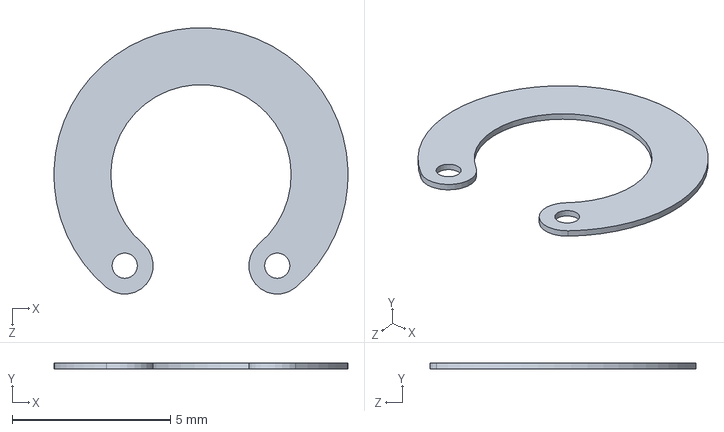
[picture p83: CAD file, 2019-10-07]
progetto/pot_contatto_sotto.SLDPRT
9.29 x 0.2 x 8.41 mm
