bombons/cad-eggbot/progetto/reggi_stepper_penna.SLDPRT

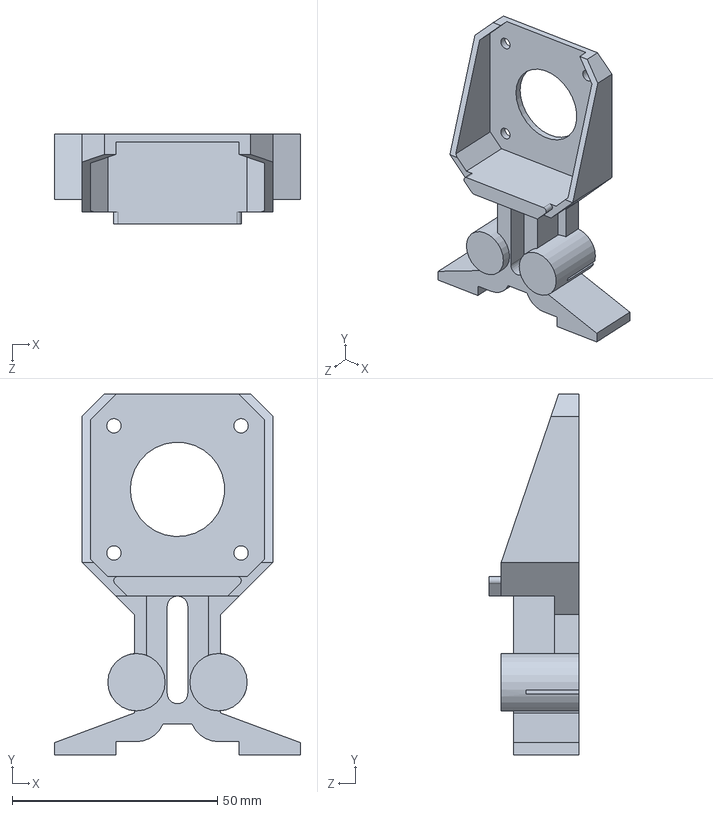
[picture p84: CAD file, 2019-10-07]
progetto/reggi_stepper_penna.SLDPRT
60.0 x 88.0 x 22.0 mm
