bombons/cad-eggbot/progetto/diodo.SLDPRT

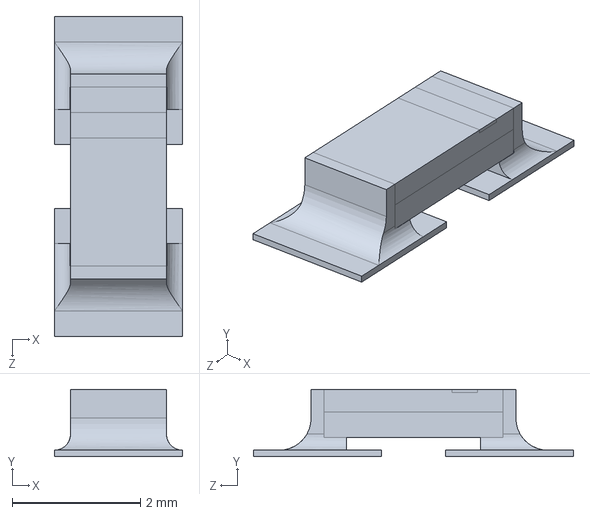
[picture p85: CAD file, 2019-10-07]
progetto/diodo.SLDPRT
2.00 x 1.05 x 5.00 mm
