bombons/cad-eggbot/progetto/porta_cuscino.SLDPRT

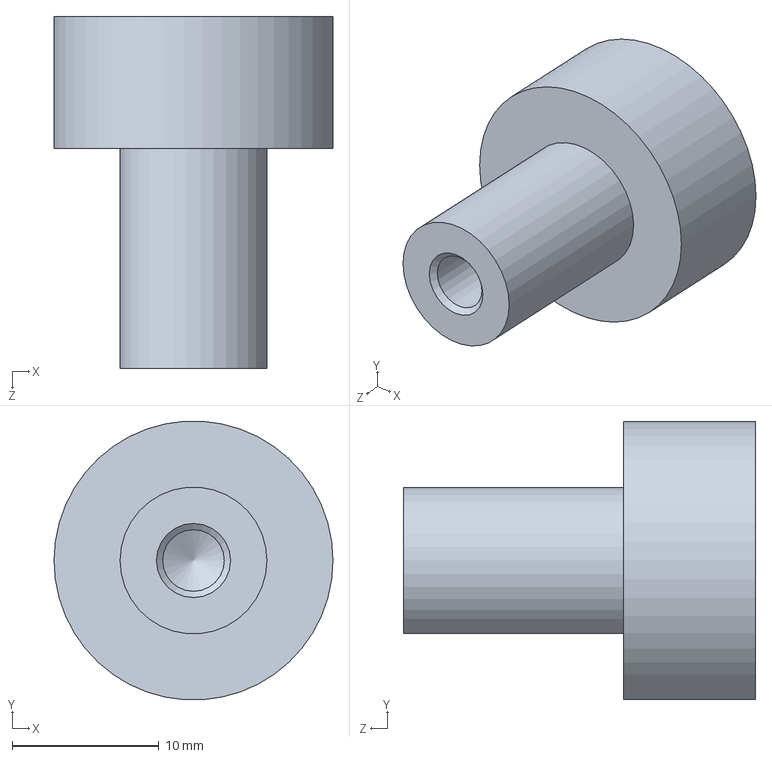
[picture p86: CAD file, 2019-10-07]
progetto/porta_cuscino.SLDPRT
19.0 x 19.0 x 24.0 mm
