bombons/cad-eggbot/progetto/pcb_resistenza.SLDPRT

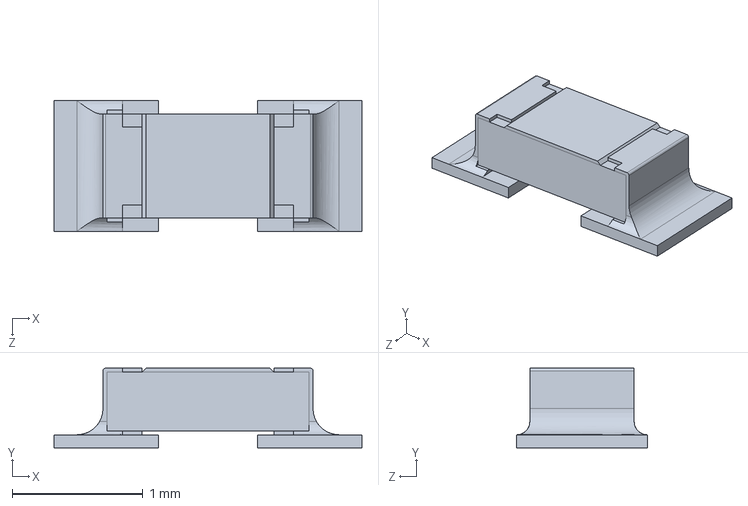
[picture p87: CAD file, 2019-10-07]
progetto/pcb_resistenza.SLDPRT
2.36 x 0.61 x 1.00 mm
