bombons/cad-eggbot/progetto/condensatore.SLDPRT

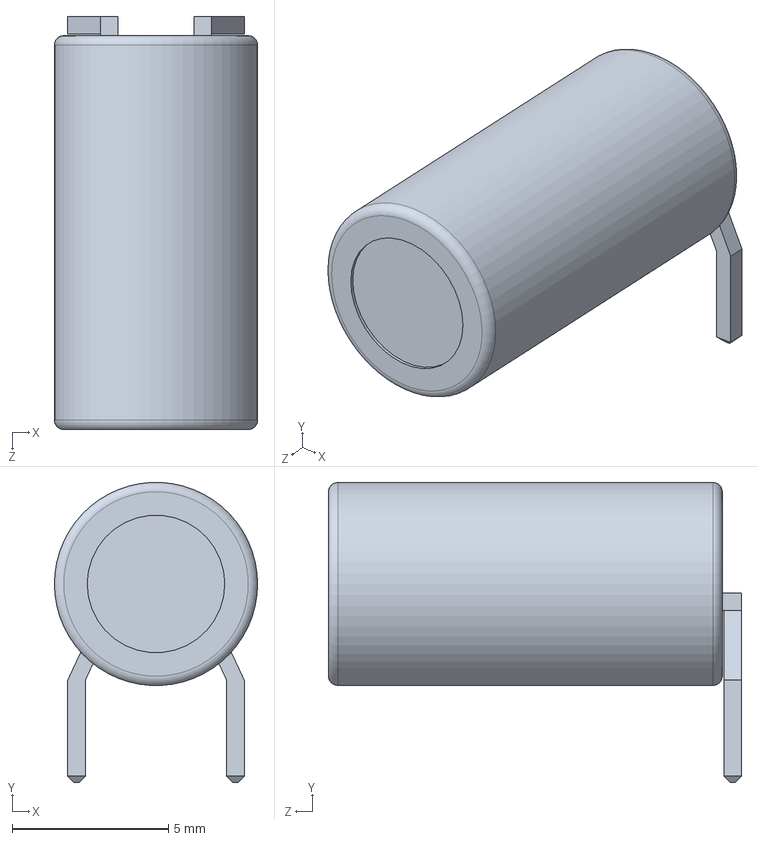
[picture p88: CAD file, 2019-10-07]
progetto/condensatore.SLDPRT
6.50 x 9.60 x 13.2 mm
