bombons/cad-eggbot/progetto/barra_filettata.SLDPRT

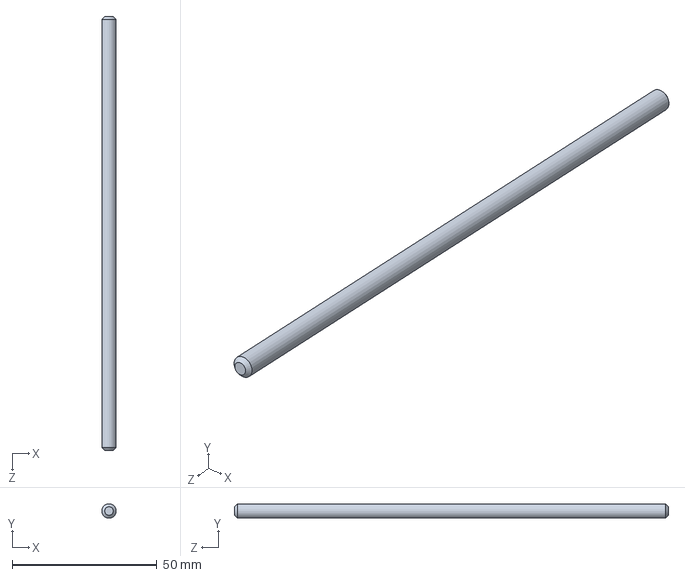
[picture p89: CAD file, 2019-10-07]
progetto/barra_filettata.SLDPRT
5.00 x 5.00 x 150.0 mm
