bombons/cad-eggbot/progetto/diodo2.SLDPRT

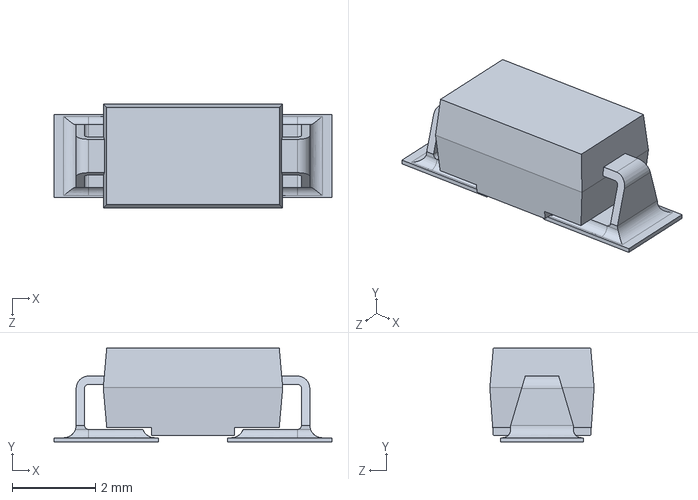
[picture p90: CAD file, 2019-10-07]
progetto/diodo2.SLDPRT
6.66 x 2.25 x 2.50 mm
