bombons/cad-eggbot/progetto/lmv.SLDPRT

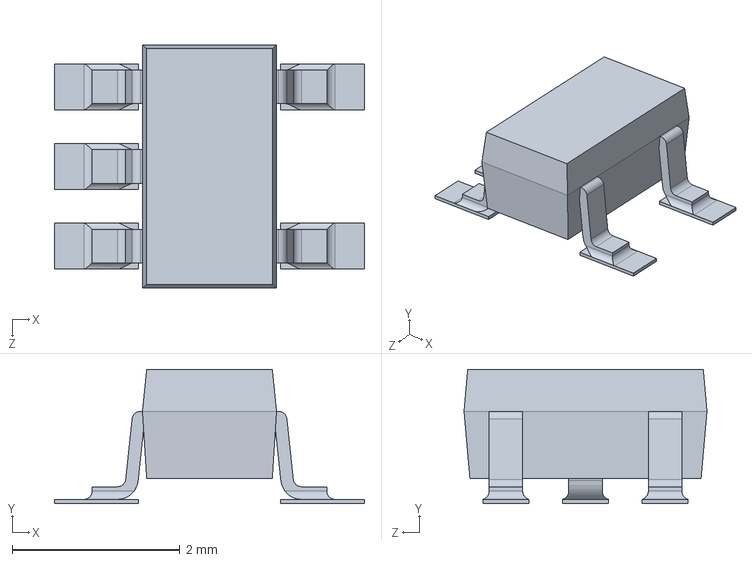
[picture p91: CAD file, 2019-10-07]
progetto/lmv.SLDPRT
3.70 x 1.60 x 2.90 mm
