bombons/cad-eggbot/progetto/2.2_16.SLDPRT

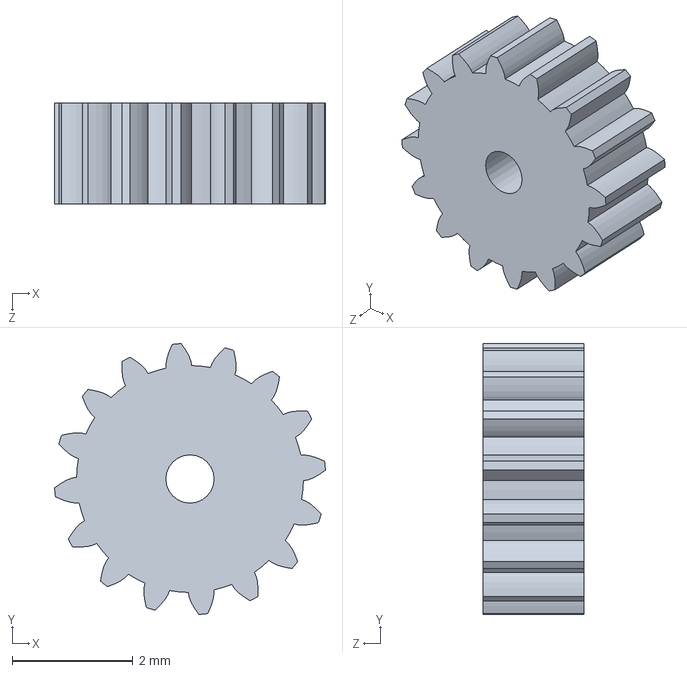
[picture p92: CAD file, 2019-10-07]
progetto/2.2_16.SLDPRT
4.49 x 4.49 x 1.67 mm
