bombons/cad-eggbot/progetto/pcb_microproc.SLDPRT

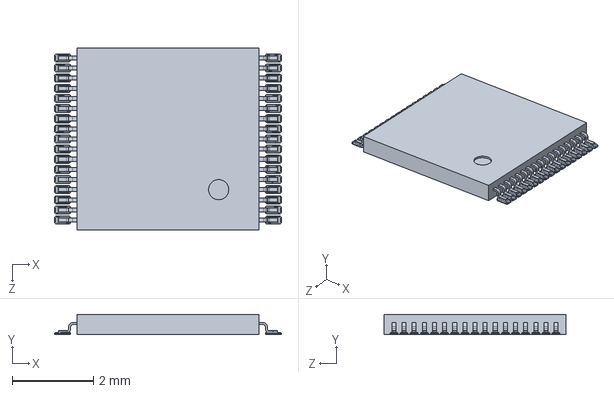
[picture p93: CAD file, 2019-10-07]
progetto/pcb_microproc.SLDPRT
5.60 x 0.5 x 4.50 mm
