bombons/cad-eggbot/progetto/pot_spazzole.SLDPRT

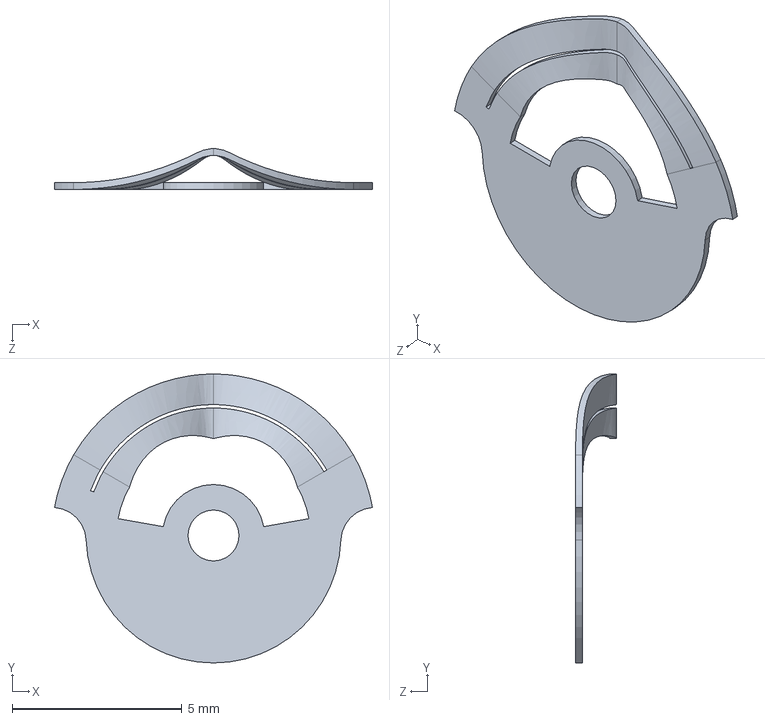
[picture p94: CAD file, 2019-10-07]
progetto/pot_spazzole.SLDPRT
9.36 x 8.50 x 1.20 mm
