bombons/cad-eggbot/progetto/blm.SLDPRT

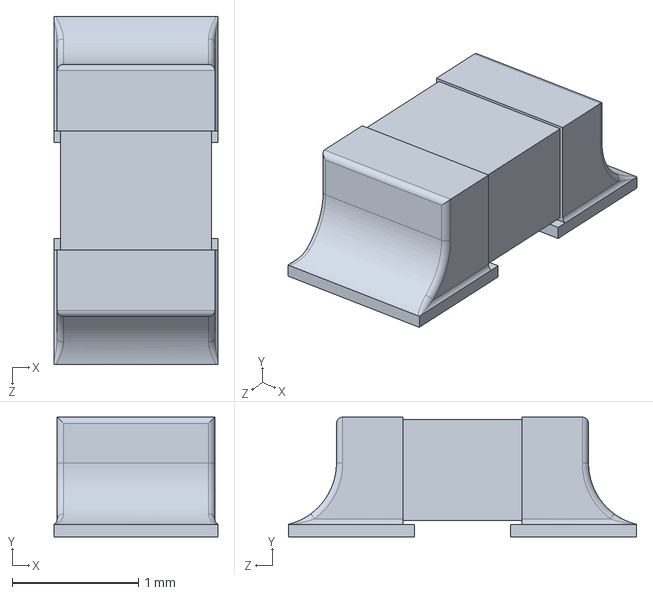
[picture p95: CAD file, 2019-10-07]
progetto/blm.SLDPRT
1.30 x 0.95 x 2.76 mm
