bombons/cad-eggbot/progetto/board_A4988.SLDPRT

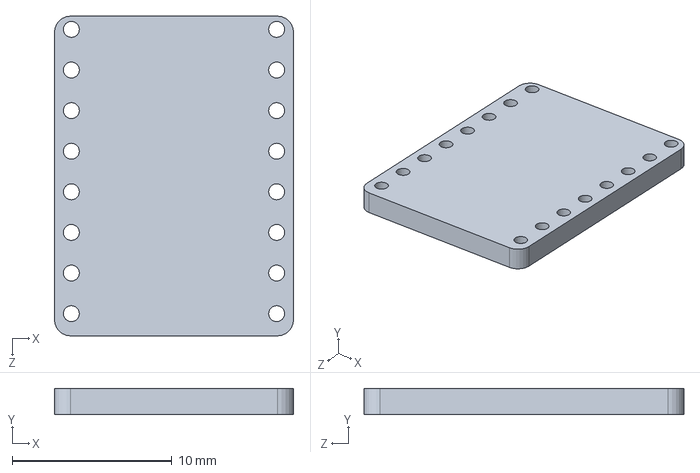
[picture p96: CAD file, 2019-10-07]
progetto/board_A4988.SLDPRT
14.9 x 1.65 x 20.0 mm
