bombons/cad-eggbot/progetto/piede_penna.SLDPRT

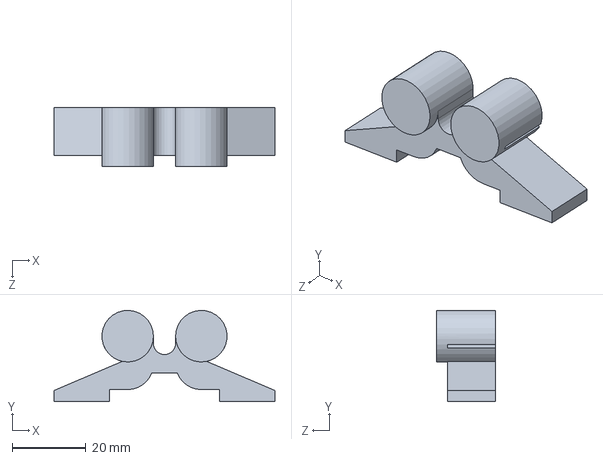
[picture p97: CAD file, 2019-10-07]
progetto/piede_penna.SLDPRT
60.0 x 24.7 x 16.0 mm
