bombons/cad-eggbot/progetto/condensatore_47uf.SLDPRT

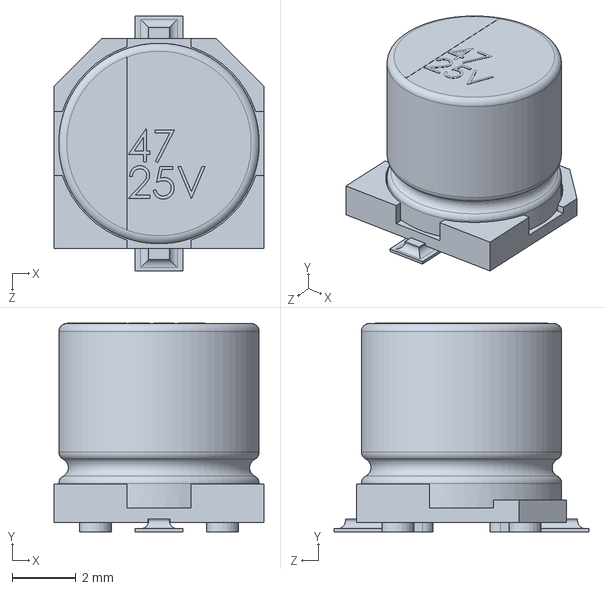
[picture p98: CAD file, 2019-10-07]
progetto/condensatore_47uf.SLDPRT
6.60 x 6.56 x 8.00 mm
