bombons/cad-eggbot/progetto/statore_magnete.SLDPRT

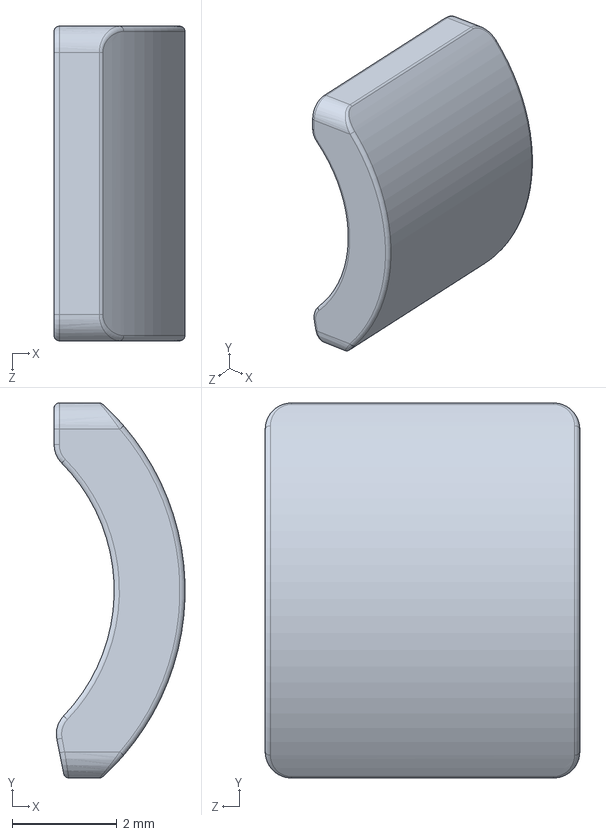
[picture p99: CAD file, 2019-10-07]
progetto/statore_magnete.SLDPRT
2.50 x 7.15 x 6.00 mm
