bombons/cad-eggbot/progetto/condensatore3.SLDPRT

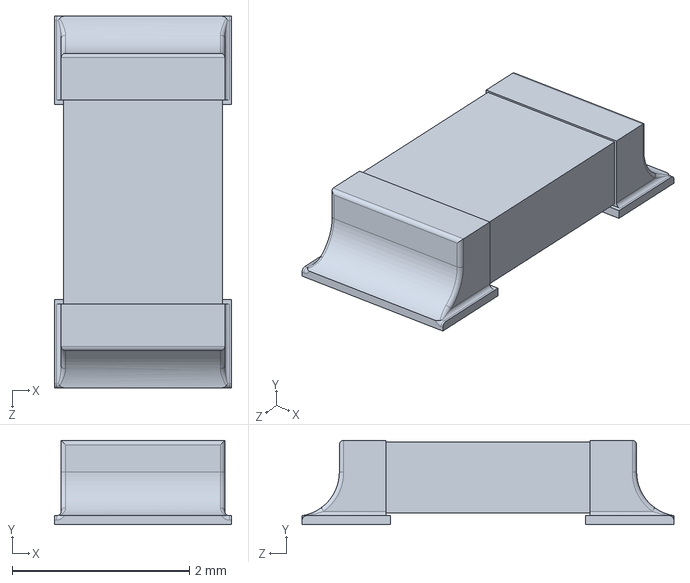
[picture p100: CAD file, 2019-10-07]
progetto/condensatore3.SLDPRT
2.00 x 0.95 x 4.20 mm
