bombons/cad-eggbot/progetto/condensatore2.SLDPRT

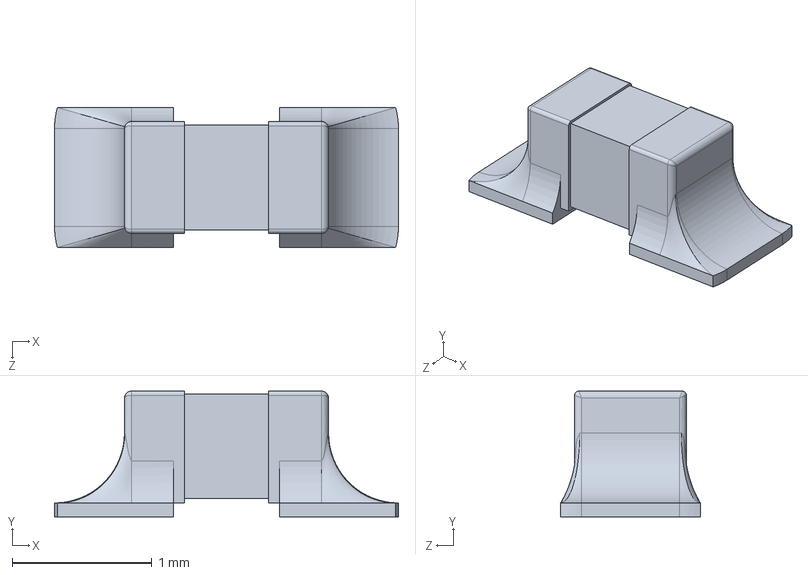
[picture p101: CAD file, 2019-10-07]
progetto/condensatore2.SLDPRT
2.46 x 0.9 x 1.00 mm
