bombons/cad-eggbot/progetto/SKF - 625 - 8,DE,AC,8_68.SLDPRT

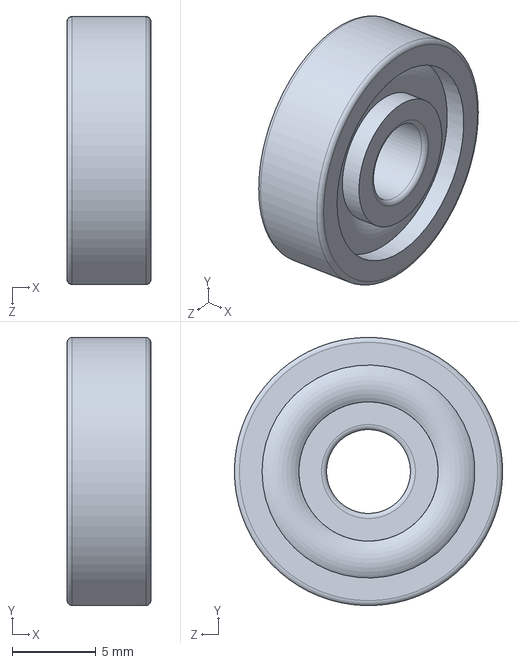
[picture p102: CAD file, 2019-10-07]
progetto/SKF - 625 - 8,DE,AC,8_68.SLDPRT
5.00 x 16.0 x 16.0 mm
