bombons/cad-eggbot/progetto/rotore_corpo_commutatore.SLDPRT

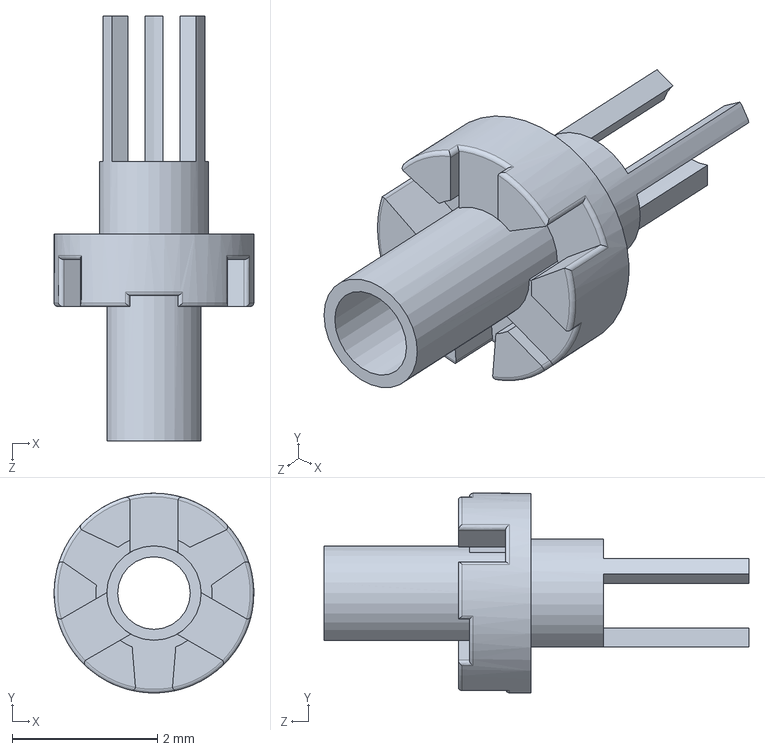
[picture p103: CAD file, 2019-10-07]
progetto/rotore_corpo_commutatore.SLDPRT
2.75 x 2.75 x 5.85 mm
