bombons/cad-eggbot/progetto/vref.SLDPRT

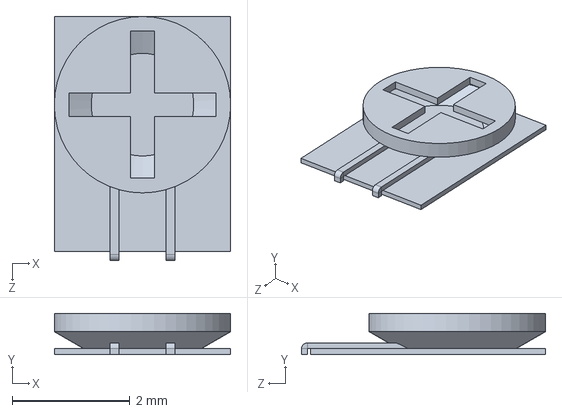
[picture p104: CAD file, 2019-10-07]
progetto/vref.SLDPRT
3.00 x 0.7 x 4.15 mm
