bombons/cad-eggbot/progetto/rotore_mozzo.SLDPRT

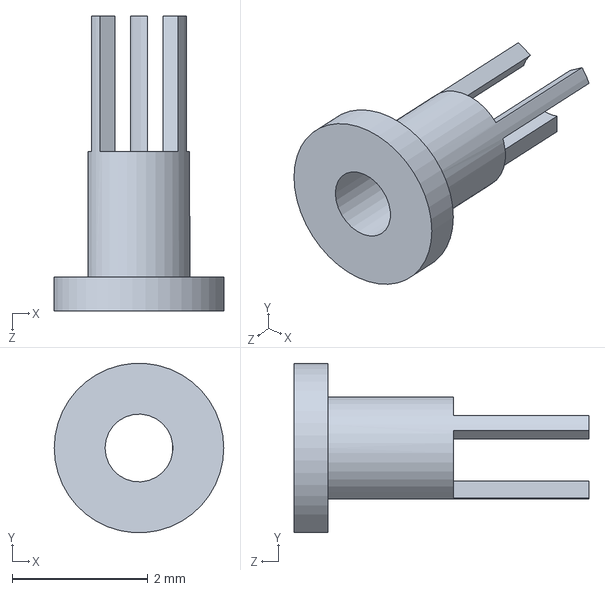
[picture p105: CAD file, 2019-10-07]
progetto/rotore_mozzo.SLDPRT
2.50 x 2.49 x 4.35 mm
