bombons/cad-eggbot/progetto/pomello_penna.SLDPRT

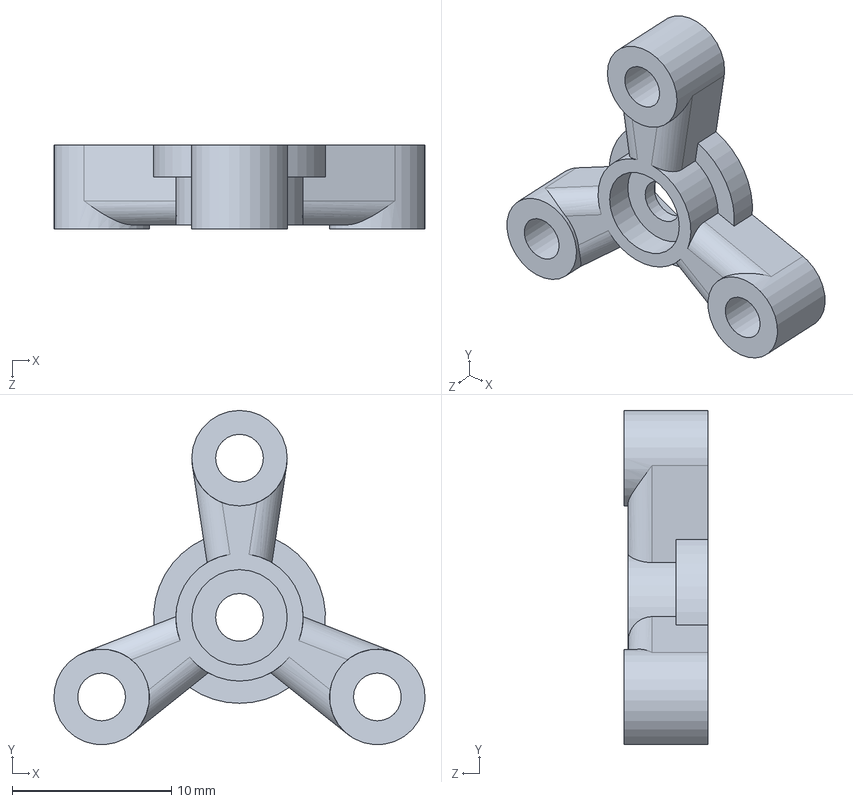
[picture p106: CAD file, 2019-10-07]
progetto/pomello_penna.SLDPRT
23.3 x 21.0 x 5.25 mm
