bombons/cad-eggbot/progetto/asta_6mm.SLDPRT

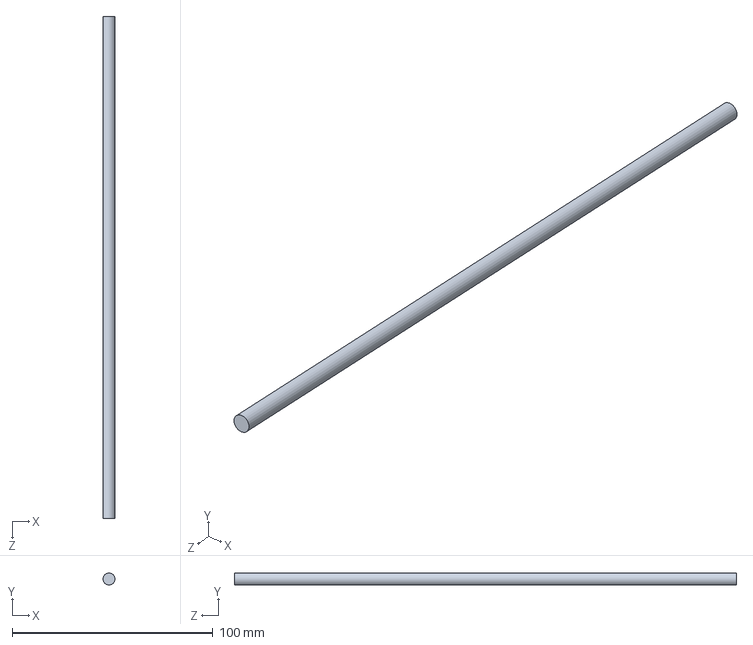
[picture p107: CAD file, 2019-10-07]
progetto/asta_6mm.SLDPRT
6.00 x 6.00 x 250.0 mm
