bombons/cad-eggbot/progetto/shell2.SLDPRT

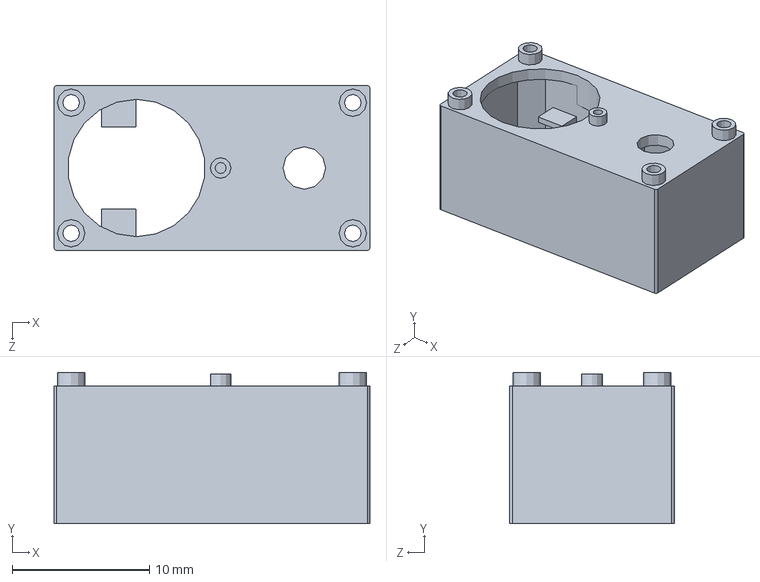
[picture p108: CAD file, 2019-10-07]
progetto/shell2.SLDPRT
23.0 x 11.0 x 12.0 mm
