bombons/cad-eggbot/progetto/shell1.SLDPRT

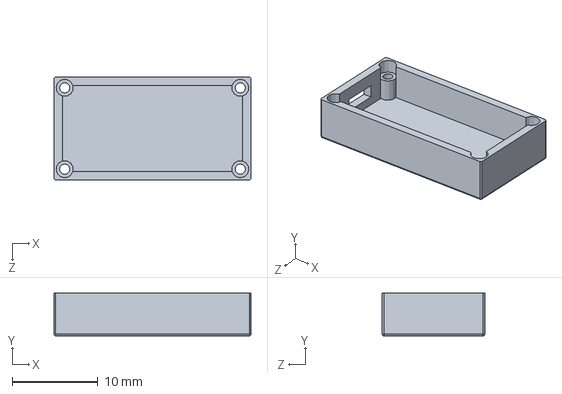
[picture p109: CAD file, 2019-10-07]
progetto/shell1.SLDPRT
23.0 x 5.00 x 12.0 mm
