bombons/cad-eggbot/progetto/piede_stepper.SLDPRT

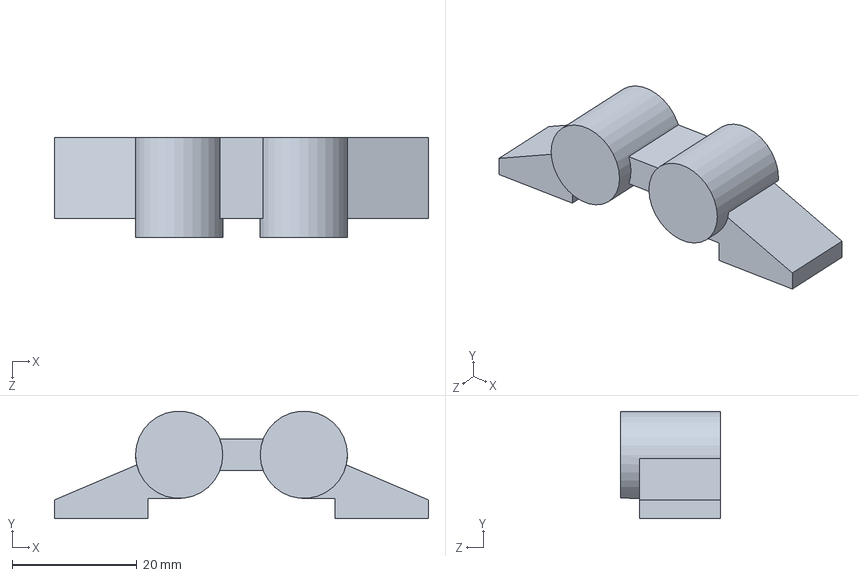
[picture p110: CAD file, 2019-10-07]
progetto/piede_stepper.SLDPRT
60.0 x 17.2 x 16.0 mm
