bombons/cad-eggbot/progetto/socket_pin.SLDPRT

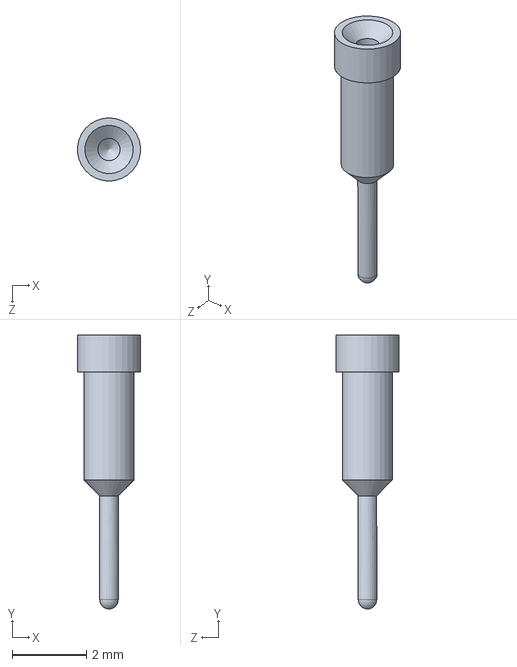
[picture p111: CAD file, 2019-10-07]
progetto/socket_pin.SLDPRT
1.69 x 7.37 x 1.70 mm
