bombons/cad-eggbot/progetto/telaio.SLDPRT

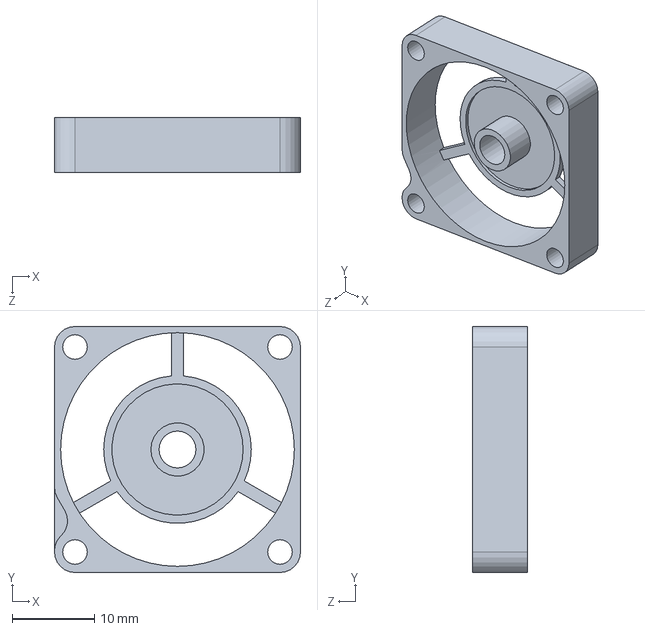
[picture p112: CAD file, 2019-10-07]
progetto/telaio.SLDPRT
30.0 x 30.0 x 6.66 mm
