bombons/cad-eggbot/progetto/magnete.SLDPRT

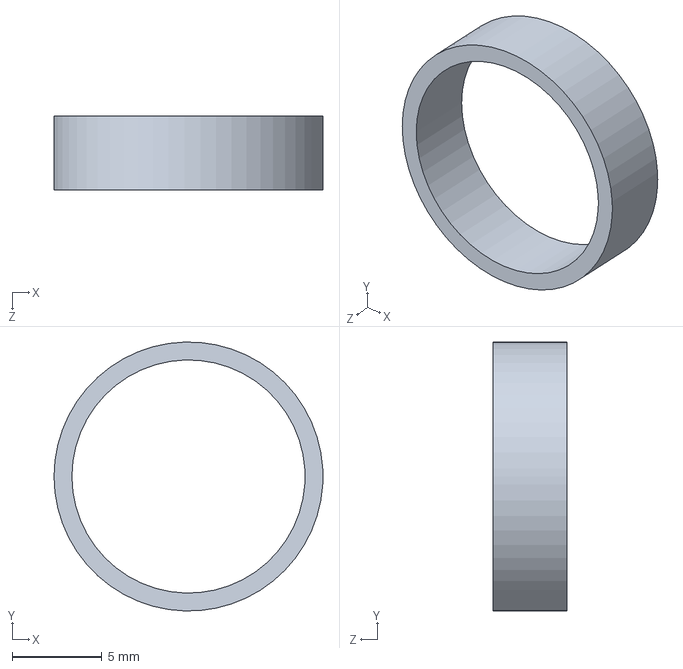
[picture p113: CAD file, 2019-10-07]
progetto/magnete.SLDPRT
15.0 x 15.0 x 4.15 mm
