bombons/cad-eggbot/progetto/intersezione_aste.SLDPRT

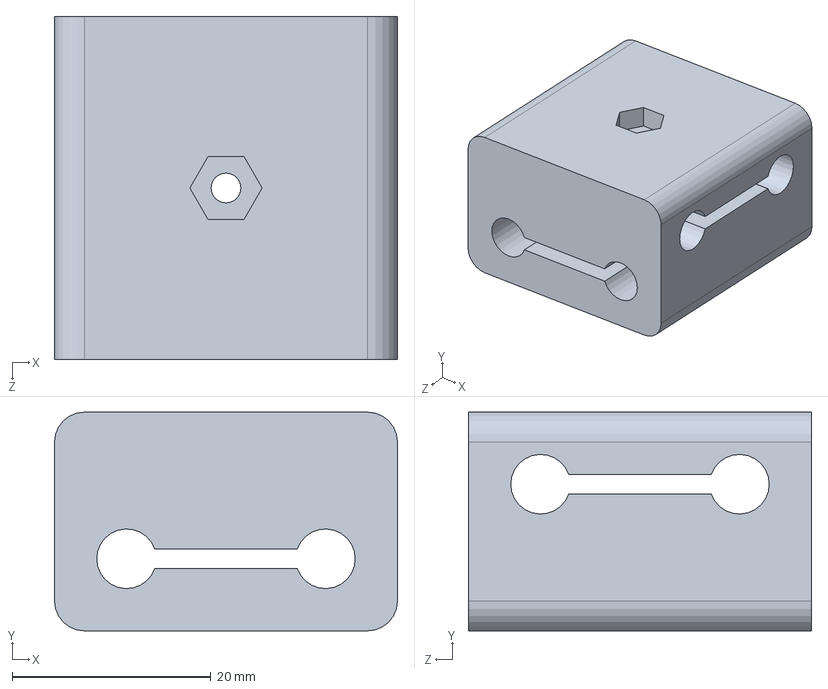
[picture p114: CAD file, 2019-10-07]
progetto/intersezione_aste.SLDPRT
34.5 x 22.0 x 34.5 mm
