bombons/cad-eggbot/progetto/lp2985.SLDPRT

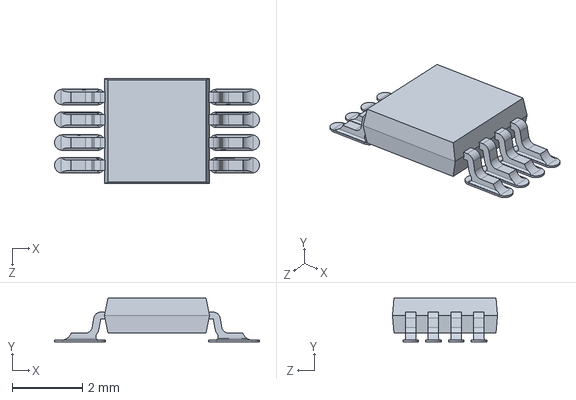
[picture p115: CAD file, 2019-10-07]
progetto/lp2985.SLDPRT
5.85 x 1.25 x 3.00 mm
