bombons/cad-eggbot/progetto/16mhz_crystal.SLDPRT

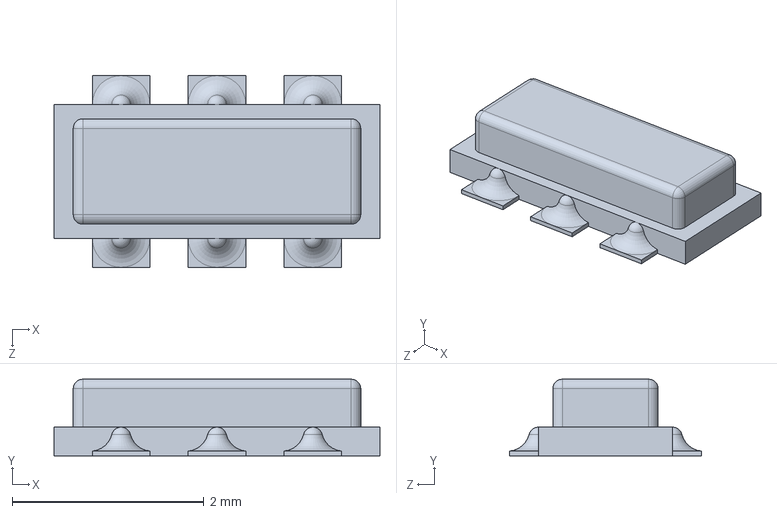
[picture p116: CAD file, 2019-10-07]
progetto/16mhz_crystal.SLDPRT
3.40 x 0.8 x 2.00 mm
