bombons/cad-eggbot/progetto/resistenza3.SLDPRT

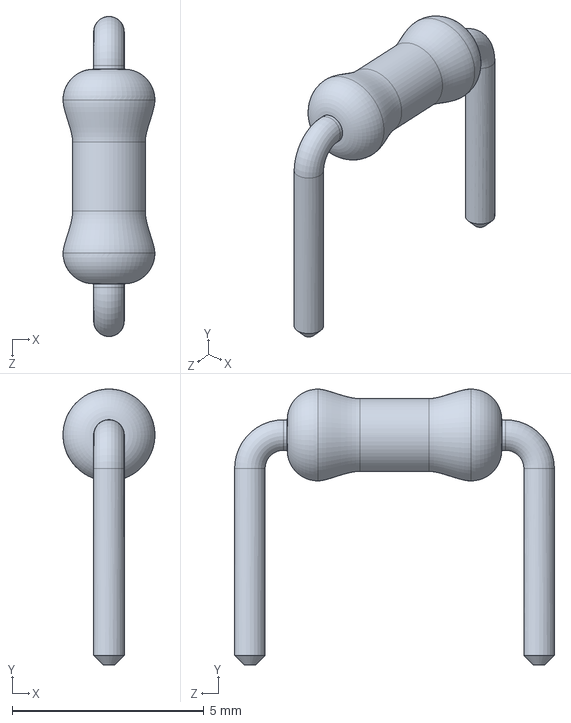
[picture p117: CAD file, 2019-10-07]
progetto/resistenza3.SLDPRT
2.40 x 7.20 x 8.35 mm
