bombons/cad-eggbot/progetto/bottone_reset_corpo.SLDPRT

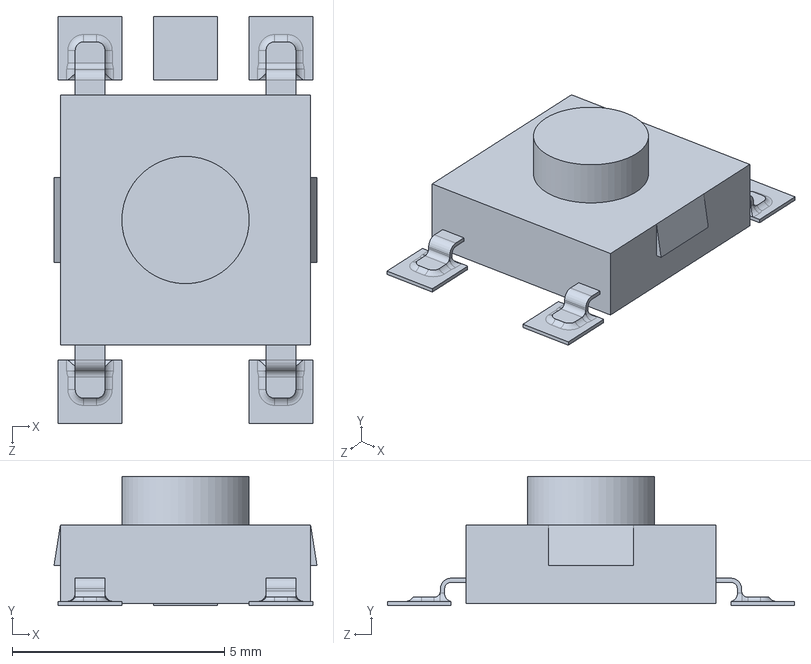
[picture p118: CAD file, 2019-10-07]
progetto/bottone_reset_corpo.SLDPRT
6.20 x 3.05 x 9.60 mm
