bombons/cad-eggbot/progetto/statore_cuscino2.SLDPRT

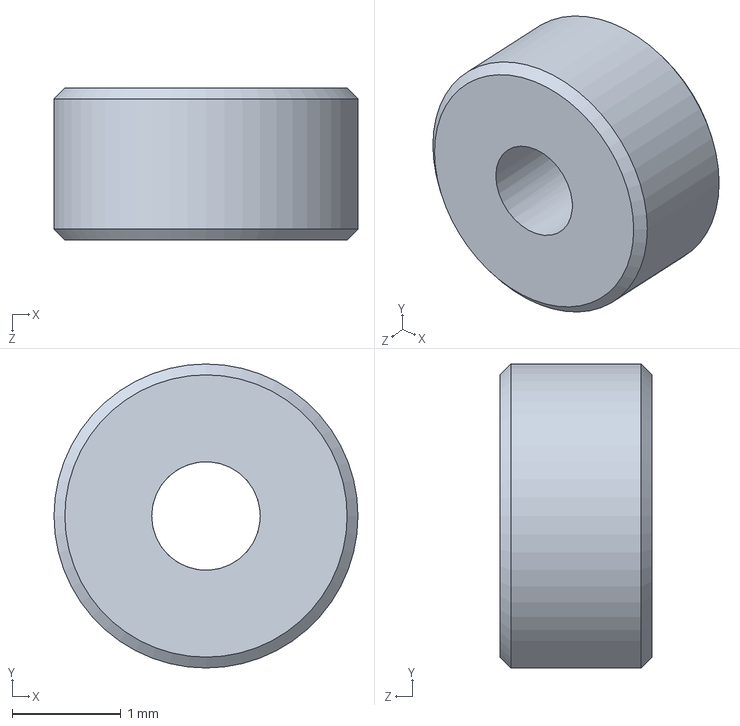
[picture p119: CAD file, 2019-10-07]
progetto/statore_cuscino2.SLDPRT
2.80 x 2.80 x 1.40 mm
