bombons/cad-eggbot/progetto/rotore_rondella3.SLDPRT

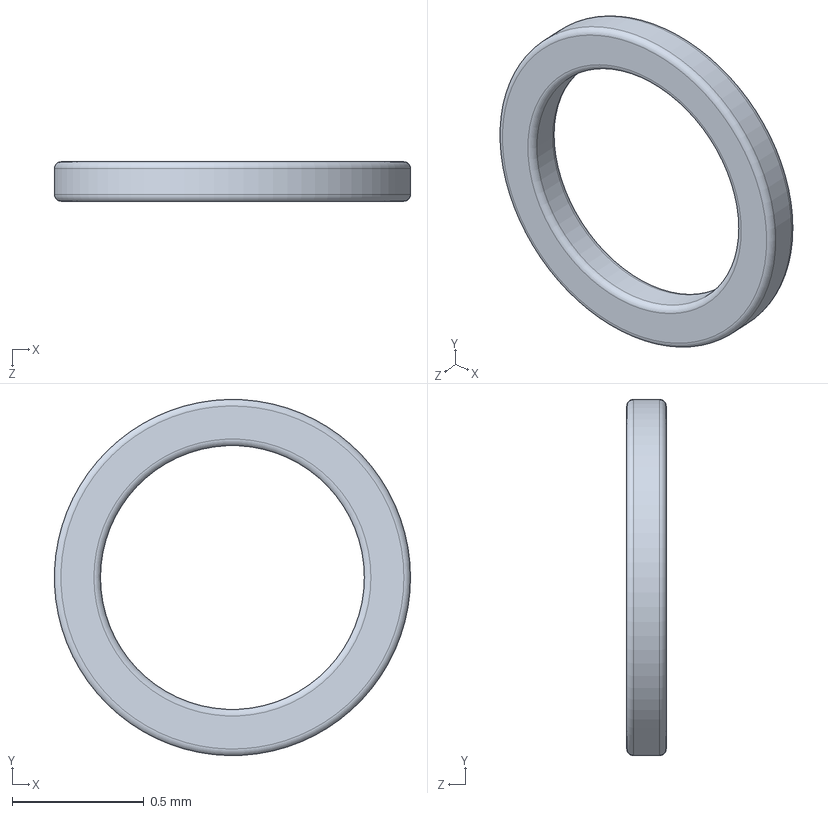
[picture p120: CAD file, 2019-10-07]
progetto/rotore_rondella3.SLDPRT
1.35 x 1.35 x 0.15 mm
