bombons/cad-eggbot/progetto/pot_piastrina.SLDPRT

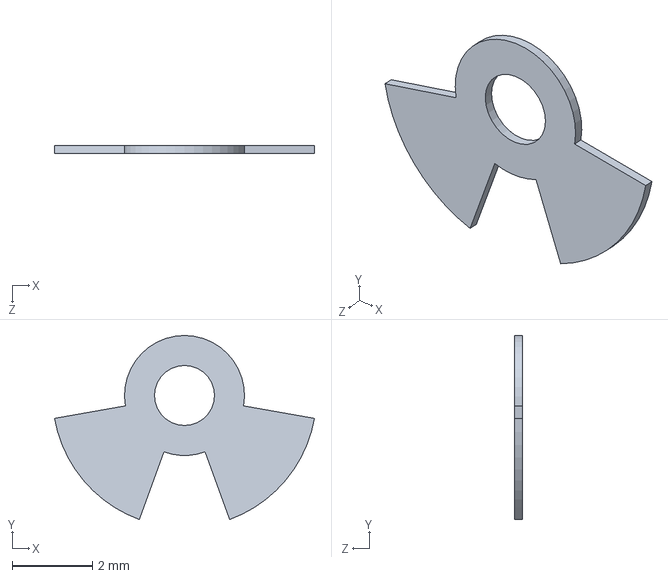
[picture p121: CAD file, 2019-10-07]
progetto/pot_piastrina.SLDPRT
6.50 x 4.60 x 0.2 mm
