bombons/cad-eggbot/progetto/statore_davanti.SLDPRT

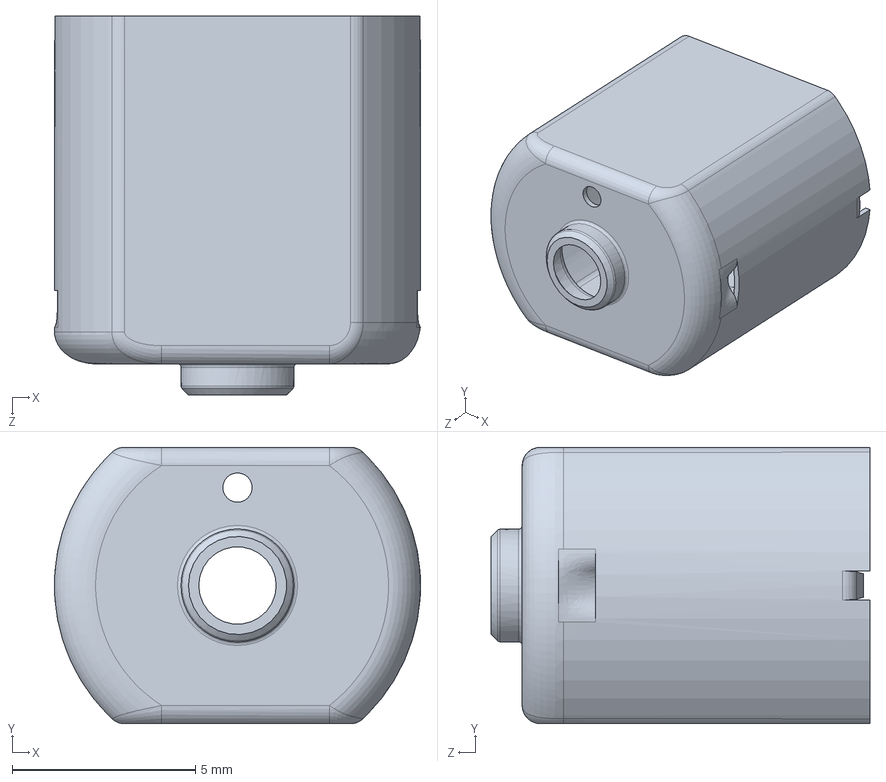
[picture p122: CAD file, 2019-10-07]
progetto/statore_davanti.SLDPRT
10.0 x 7.55 x 10.4 mm
