bombons/cad-eggbot/progetto/usb_corpo.SLDPRT

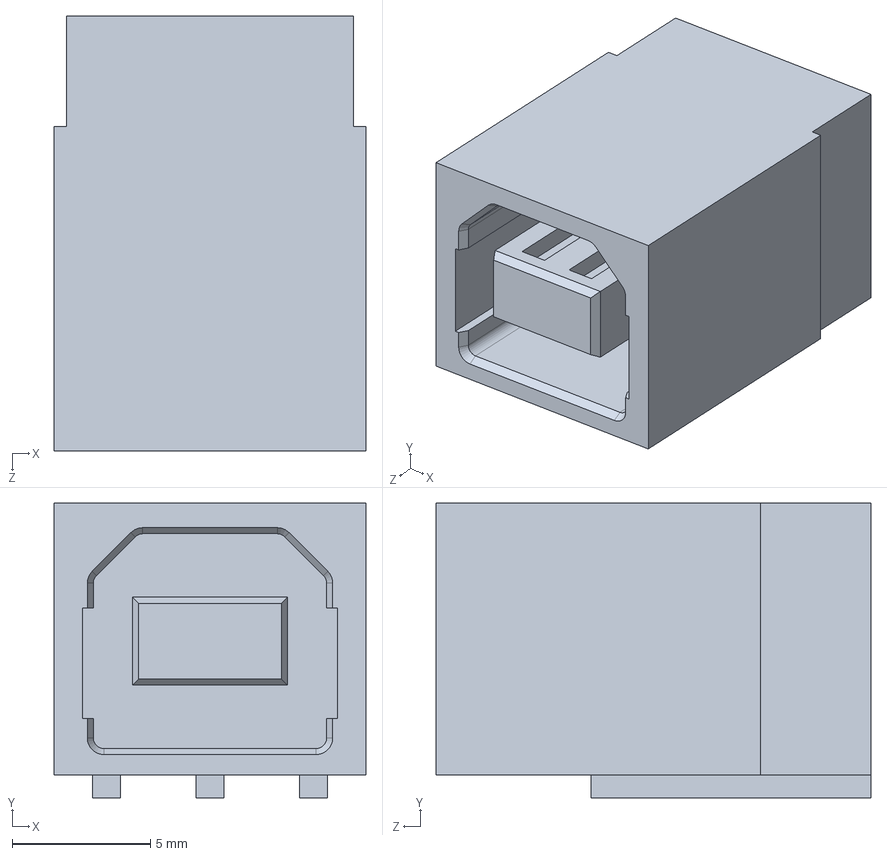
[picture p123: CAD file, 2019-10-07]
progetto/usb_corpo.SLDPRT
11.3 x 10.7 x 15.8 mm
