bombons/cad-eggbot/progetto/paletta.SLDPRT

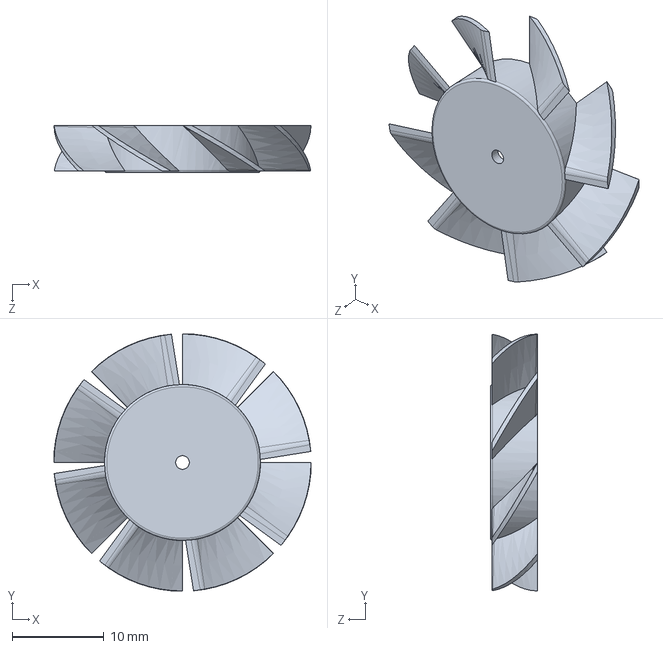
[picture p124: CAD file, 2019-10-07]
progetto/paletta.SLDPRT
28.0 x 28.0 x 5.16 mm
