bombons/cad-eggbot/progetto/vite_m3_20mm.SLDPRT

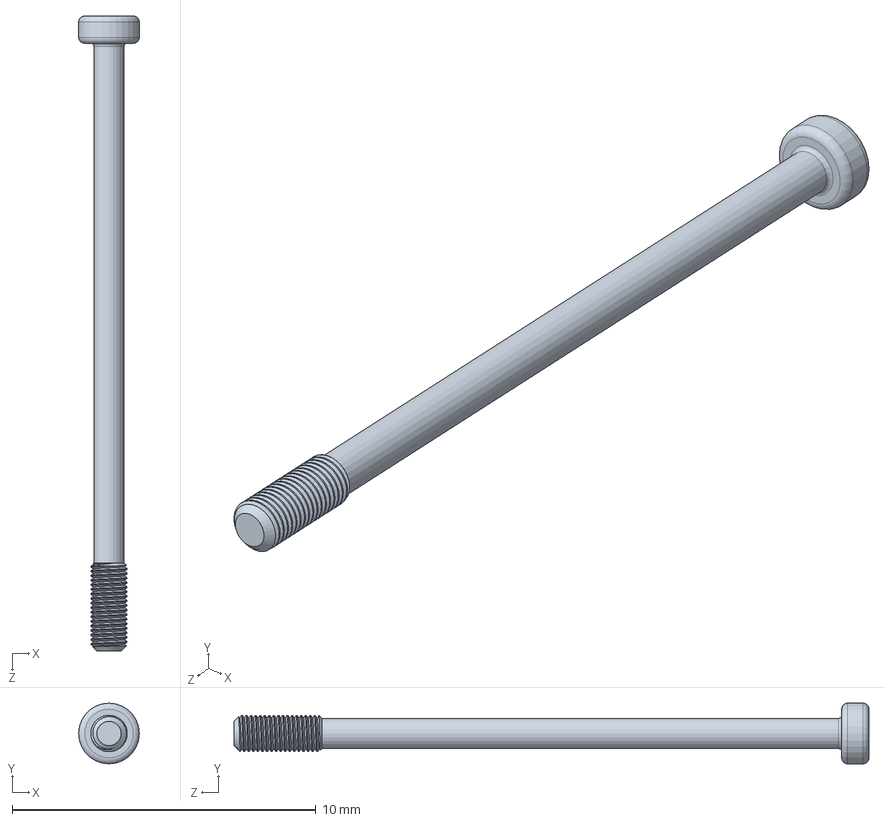
[picture p125: CAD file, 2019-10-07]
progetto/vite_m3_20mm.SLDPRT
2.00 x 2.00 x 20.9 mm
