bombons/cad-eggbot/progetto/fusibile.SLDPRT

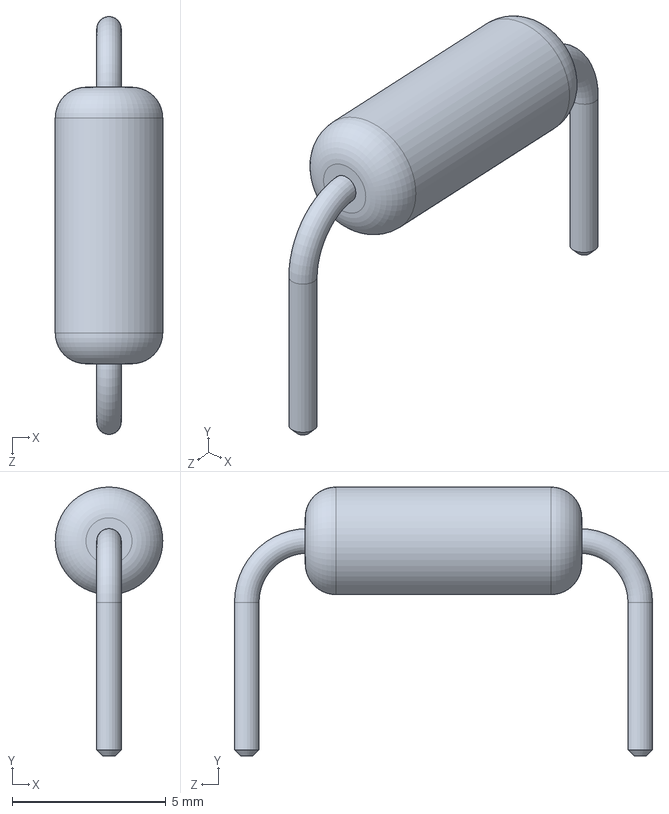
[picture p126: CAD file, 2019-10-07]
progetto/fusibile.SLDPRT
3.50 x 8.75 x 13.6 mm
