bombons/cad-eggbot/progetto/pot_cuscino.SLDPRT

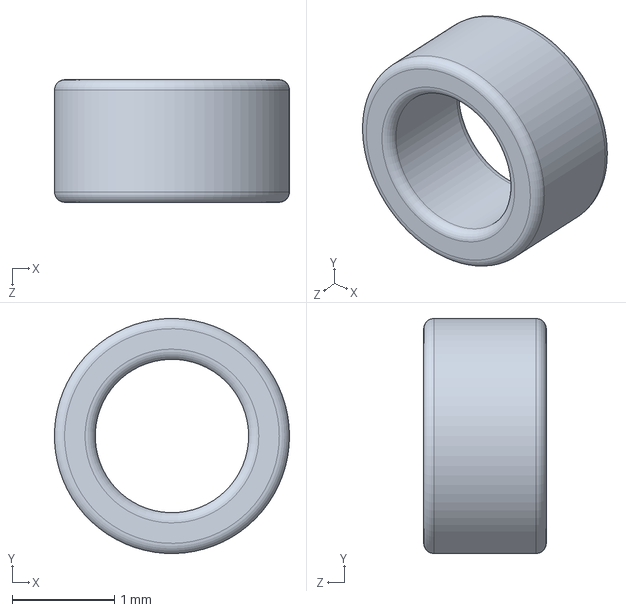
[picture p127: CAD file, 2019-10-07]
progetto/pot_cuscino.SLDPRT
2.30 x 2.30 x 1.20 mm
