bombons/cad-eggbot/progetto/port.SLDPRT

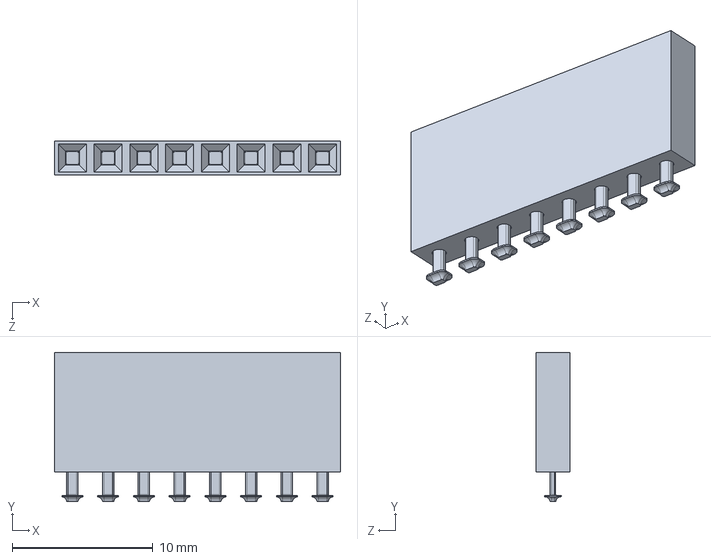
[picture p128: CAD file, 2019-10-07]
progetto/port.SLDPRT
20.3 x 10.6 x 2.41 mm
